baz-snow-ss/Voron-2.4-R2/Endstops/1eed2b93114540ddb6c84c9f8e0066f0.png

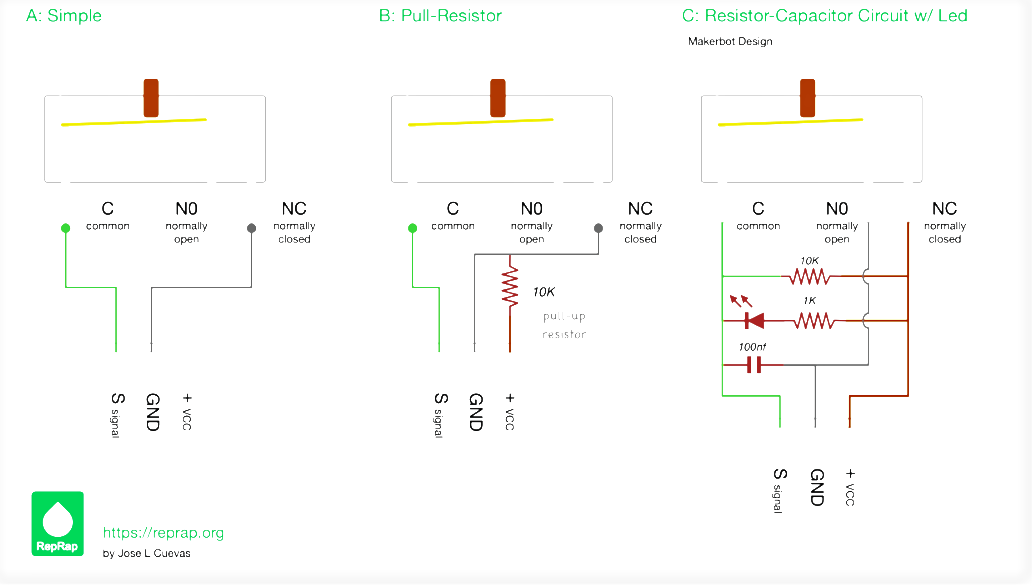
Endstops/1eed2b93114540ddb6c84c9f8e0066f0.png
