baz-snow-ss/Voron-2.4-R2/Endstops/c754031926eb4f4ea1a9c7ecbcfd5318.png

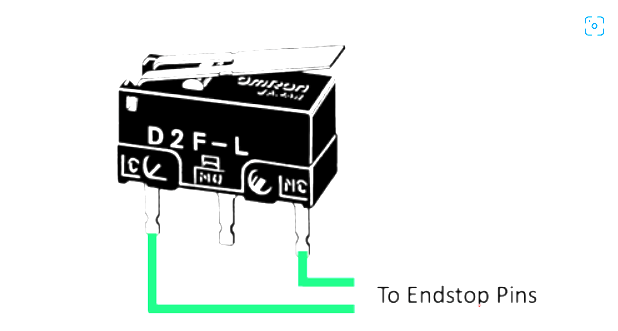
Endstops/c754031926eb4f4ea1a9c7ecbcfd5318.png
