baz-snow-ss/Voron-2.4-R2/Pictures/IMG20230324204420.jpg

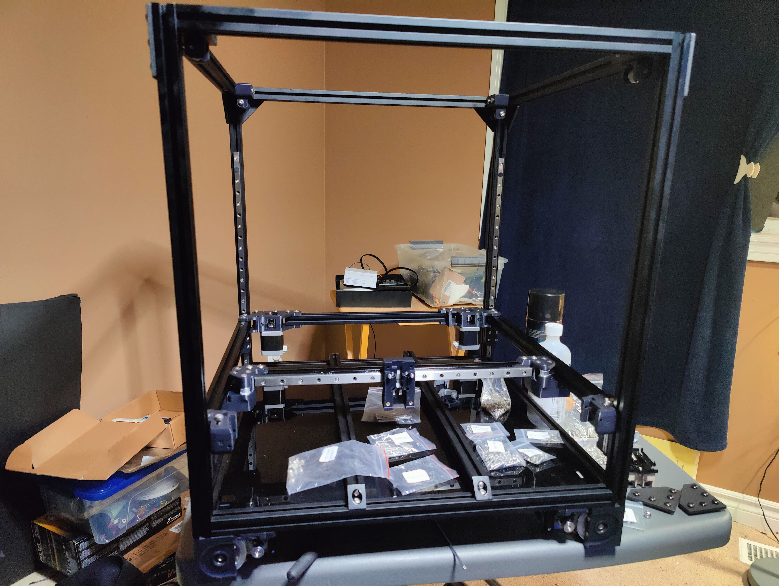
Pictures/IMG20230324204420.jpg
