baz-snow-ss/Voron-2.4-R2/Pictures/IMG20230408150425.jpg

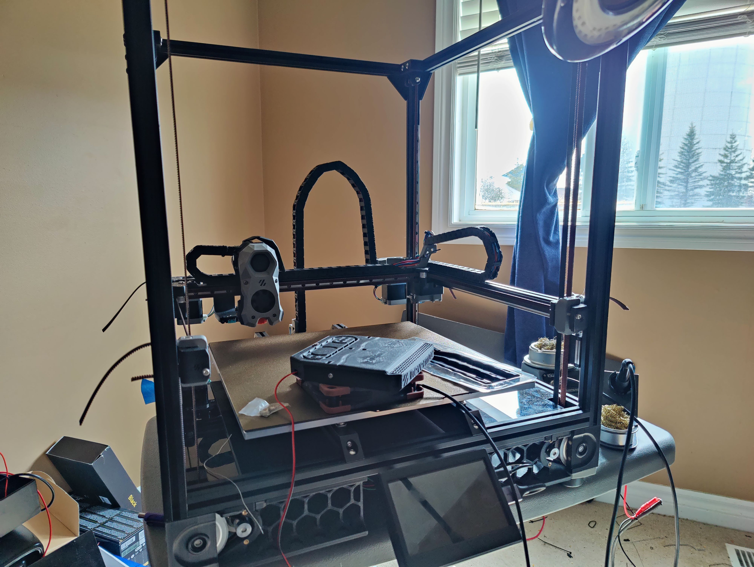
Pictures/IMG20230408150425.jpg
