baz-snow-ss/Voron-2.4-R2/Pictures/IMG20230410012818.jpg

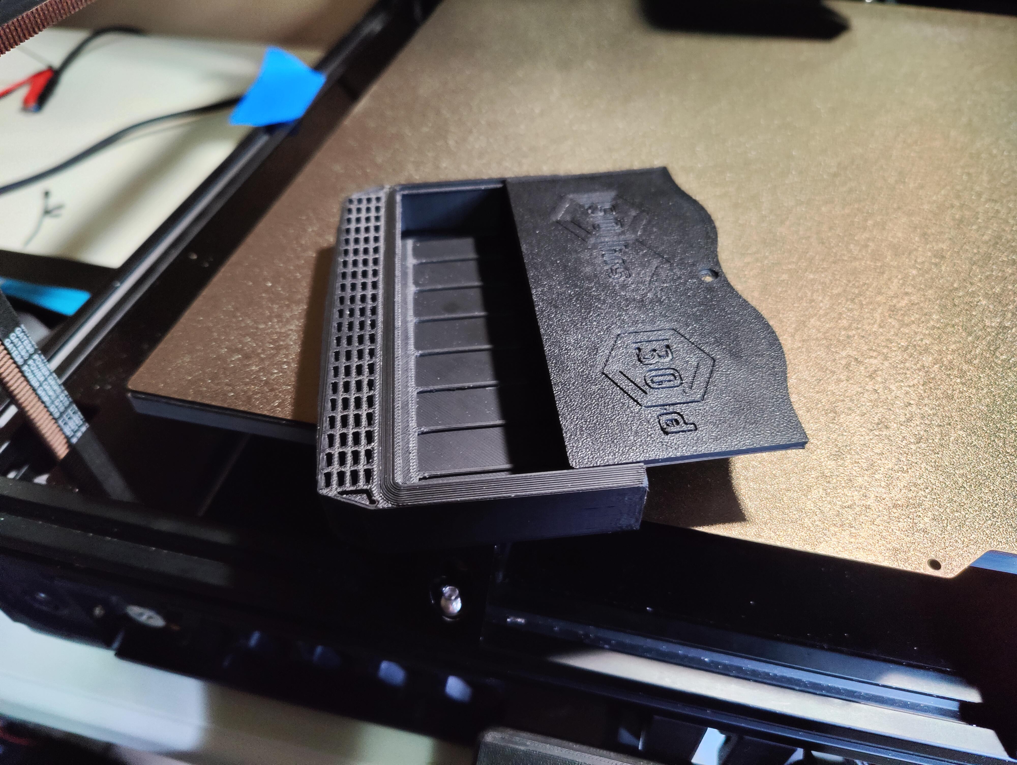
Pictures/IMG20230410012818.jpg
