baz-snow-ss/Voron-2.4-R2/Pictures/IMG20230410013023.jpg

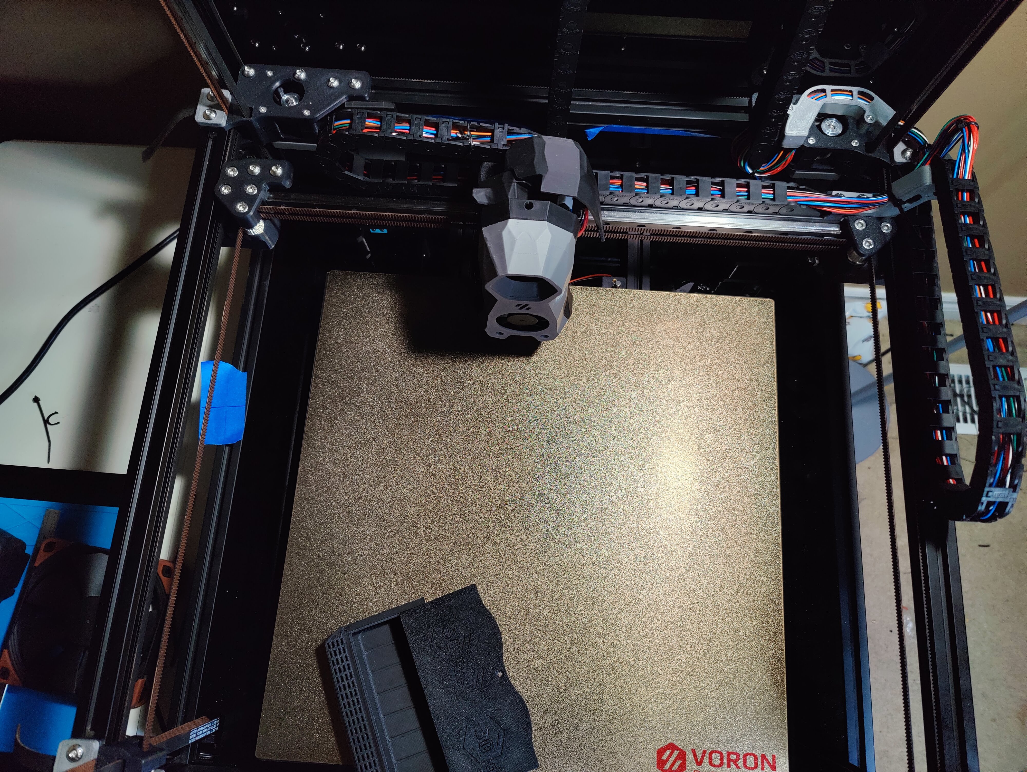
Pictures/IMG20230410013023.jpg
