baz-snow-ss/Voron-2.4-R2/Pictures/IMG20230415213202.jpg

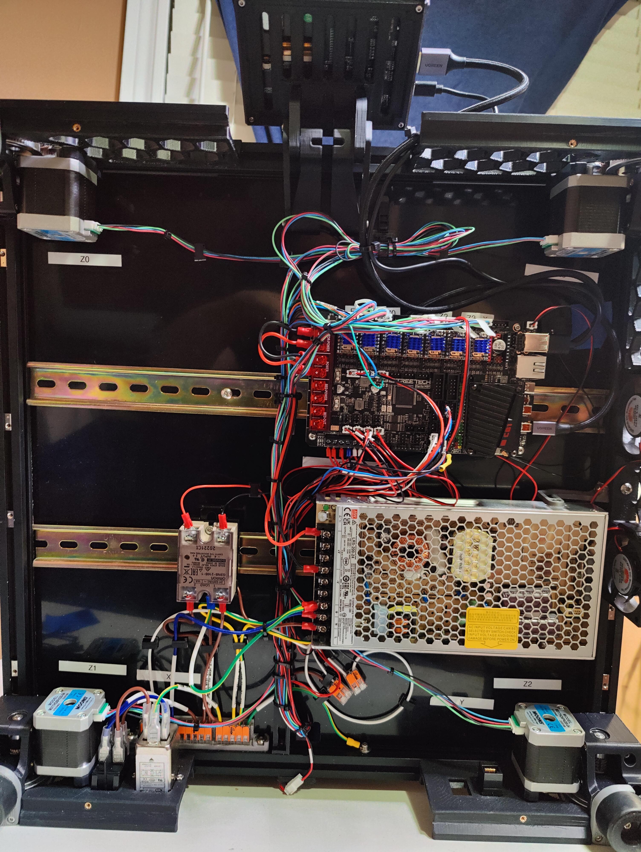
Pictures/IMG20230415213202.jpg
