baz-snow-ss/Voron-2.4-R2/Pictures/IMG20230418011041.jpg

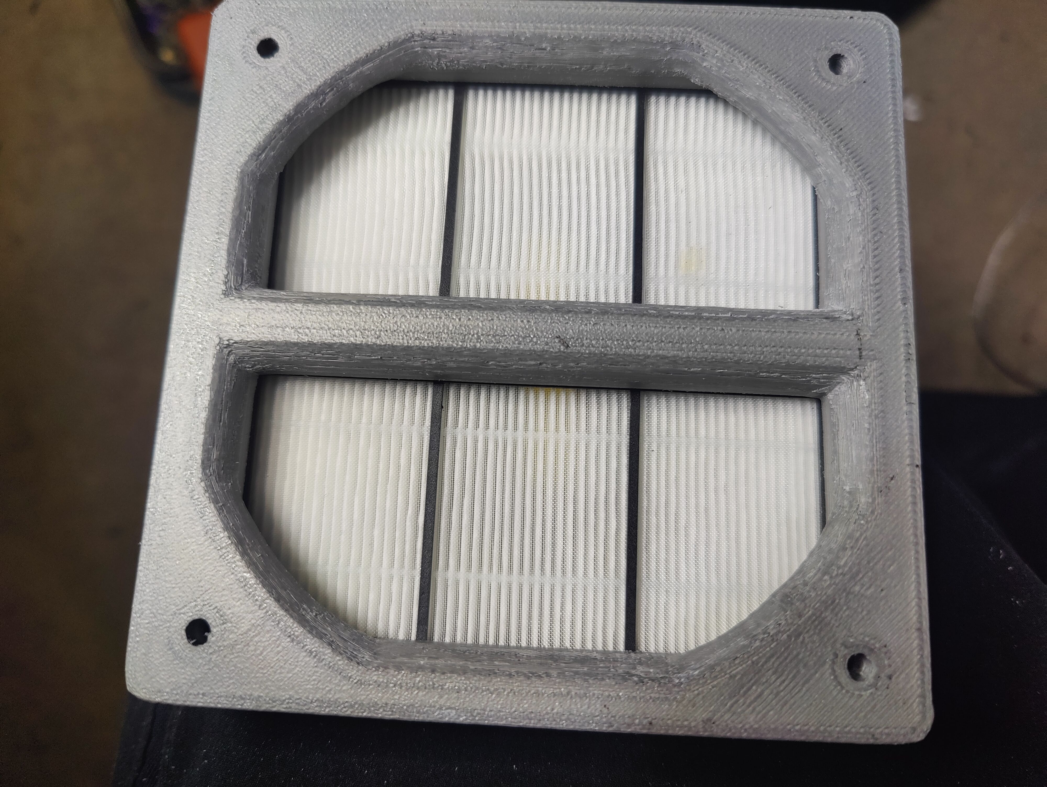
Pictures/IMG20230418011041.jpg
