baz-snow-ss/Voron-2.4-R2/Pictures/IMG20230419014356.jpg

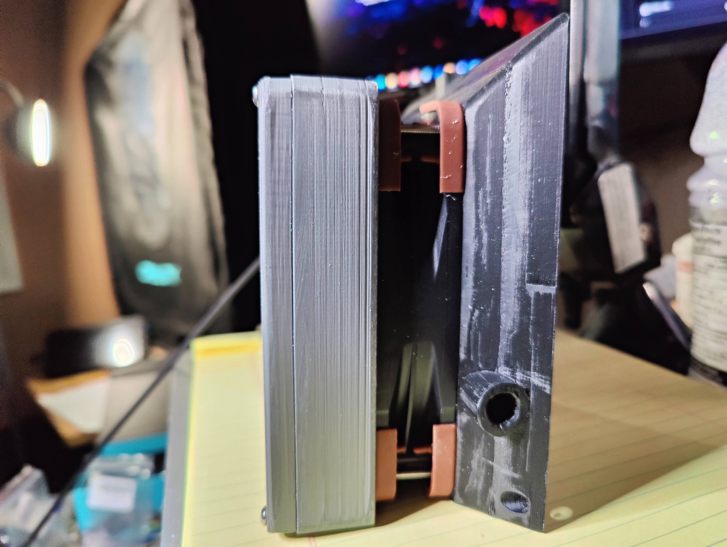
Pictures/IMG20230419014356.jpg
