baz-snow-ss/Voron-2.4-R2/Pictures/IMG20230423050257.jpg

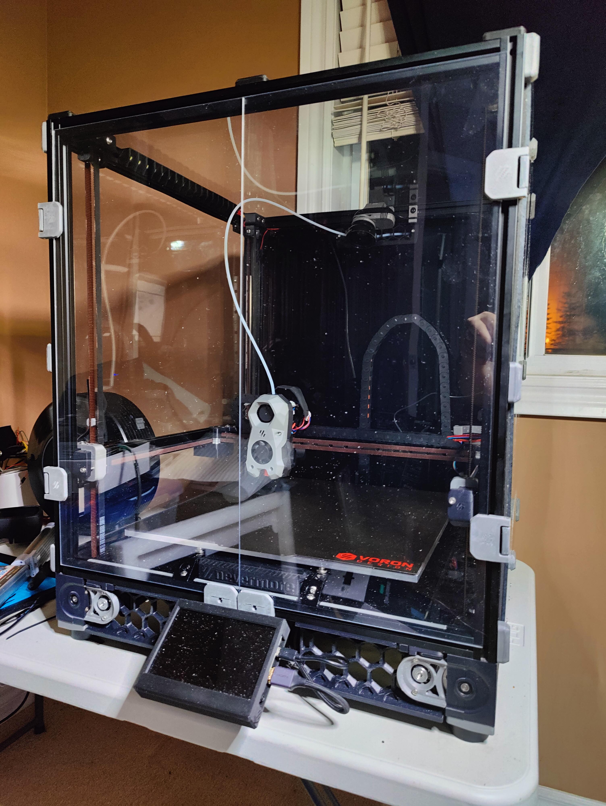
Pictures/IMG20230423050257.jpg
