baz-snow-ss/Voron-2.4-R2/Pictures/IMG20230423050415.jpg

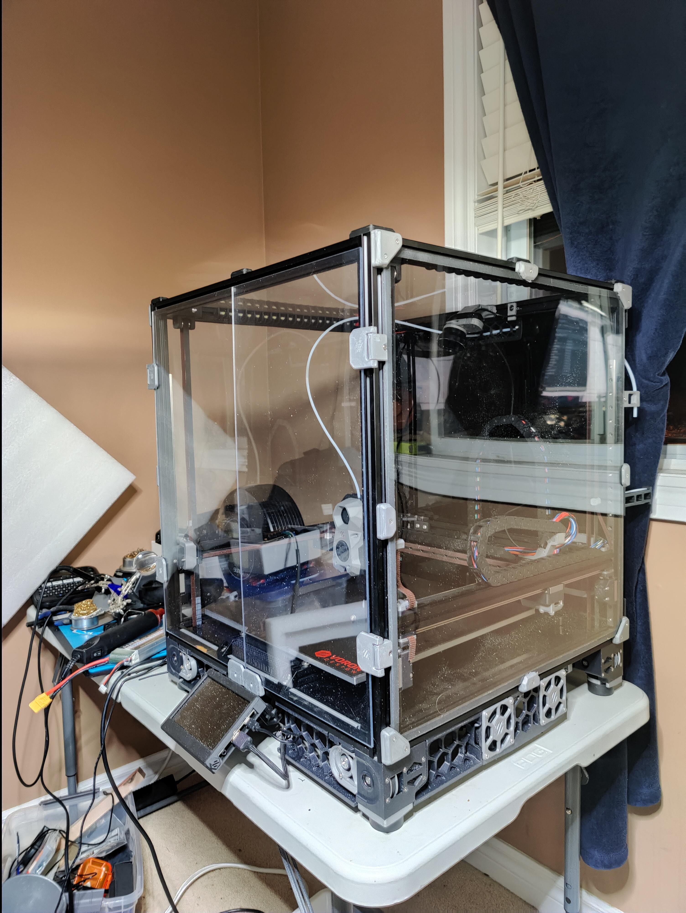
Pictures/IMG20230423050415.jpg
