baz-snow-ss/Voron-2.4-R2/Pictures/IMG20230425162826.jpg

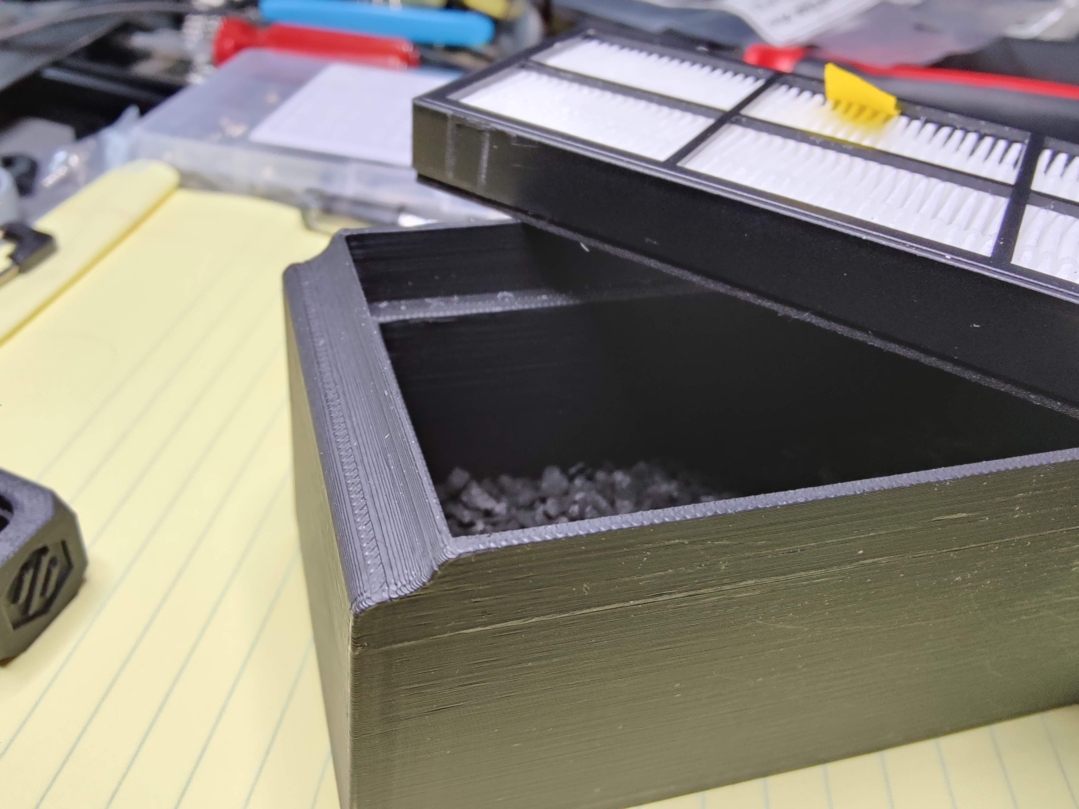
Pictures/IMG20230425162826.jpg
