baz-snow-ss/Voron-2.4-R2/Pictures/IMG20230511183152.jpg

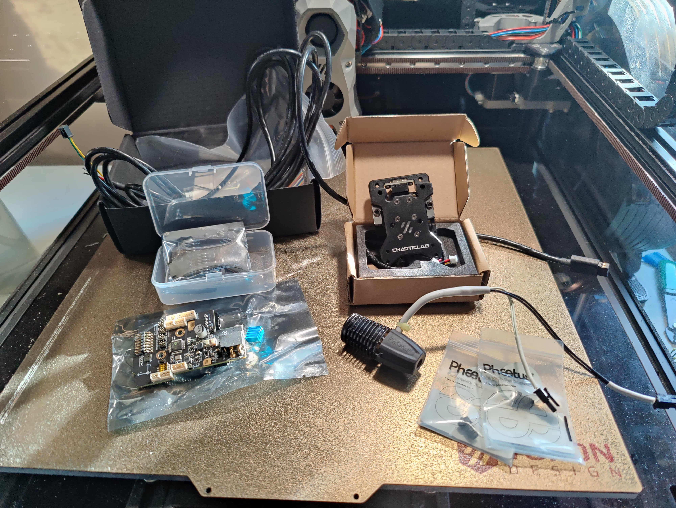
Pictures/IMG20230511183152.jpg
