baz-snow-ss/Voron-2.4-R2/STL/2020_Extrusion_profile_cover/images/395db7963a54a1277b0446aee03f2c51.jpg

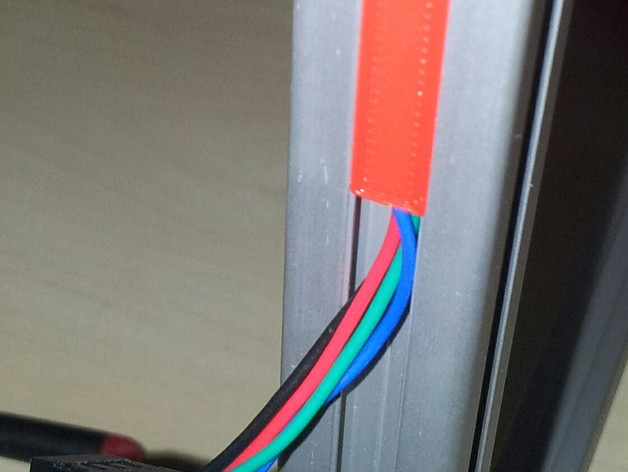
STL/2020_Extrusion_profile_cover/images/395db7963a54a1277b0446aee03f2c51.jpg
