baz-snow-ss/Voron-2.4-R2/STL/2020_Extrusion_profile_cover/images/Nut_6_Abdeckung_-_20.jpg

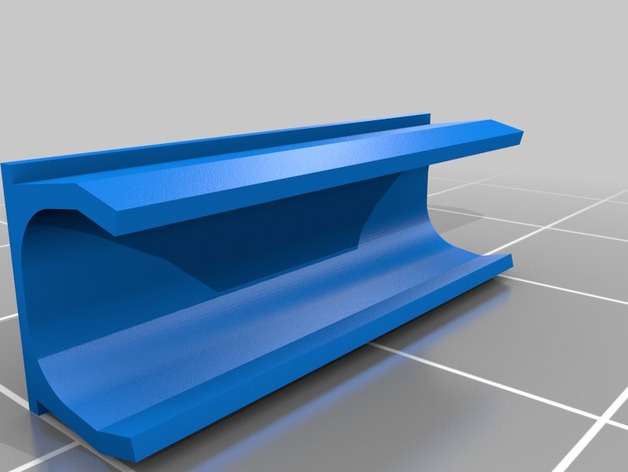
STL/2020_Extrusion_profile_cover/images/Nut_6_Abdeckung_-_20.jpg
