baz-snow-ss/Voron-2.4-R2/STL/Klicky-Probe-/Photos/klicky_base.jpg

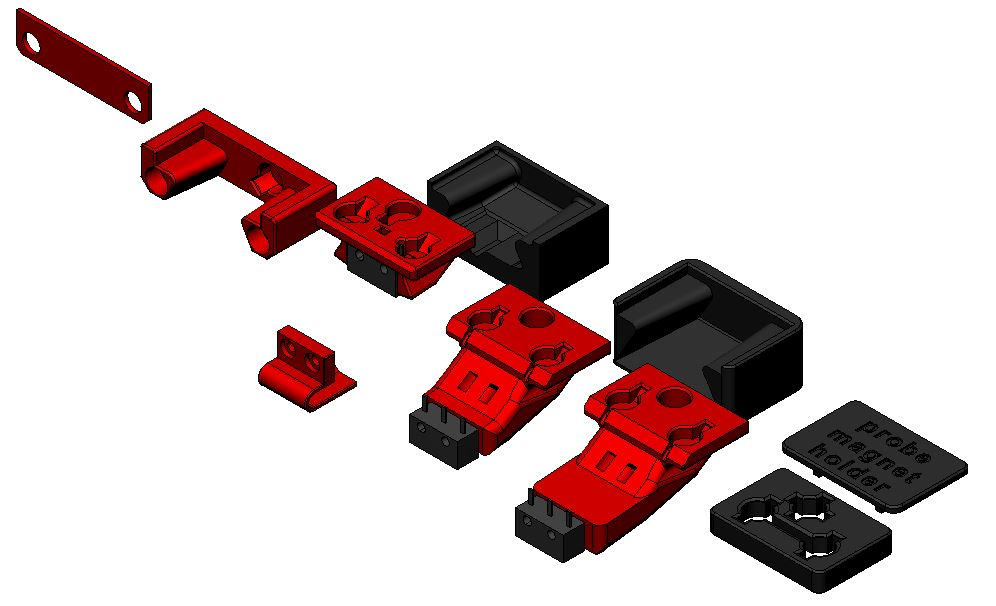
STL/Klicky-Probe-/Photos/klicky_base.jpg
