baz-snow-ss/Voron-2.4-R2/STL/LGX_Lite_Stealthburner_ERCF/IMAGES/IMG_02.png

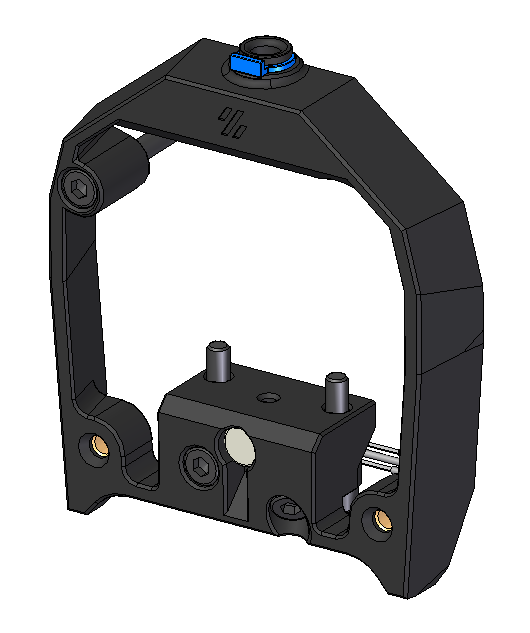
STL/LGX_Lite_Stealthburner_ERCF/IMAGES/IMG_02.png
