baz-snow-ss/Voron-2.4-R2/STL/Nevermore_Micro-master/images/DUO_COMBINED_render2.png

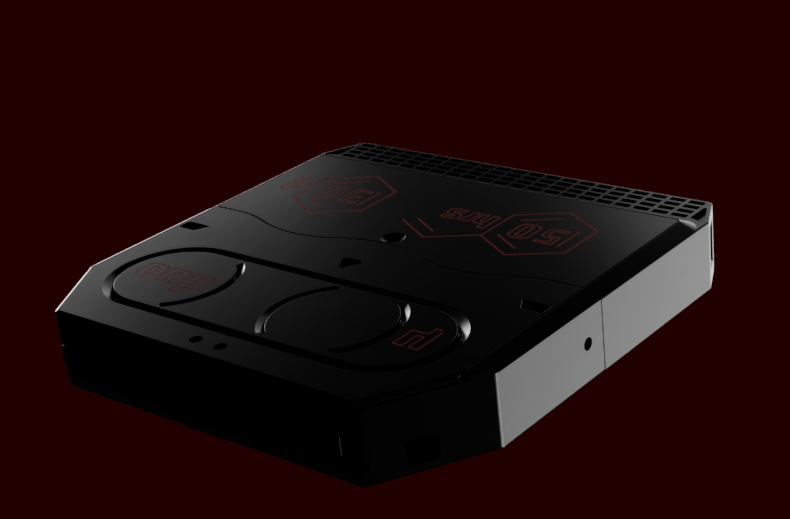
STL/Nevermore_Micro-master/images/DUO_COMBINED_render2.png
