baz-snow-ss/Voron-2.4-R2/STL/Nevermore_Micro-master/images/emitted-voc.jpg

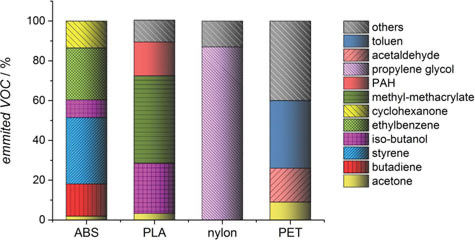
STL/Nevermore_Micro-master/images/emitted-voc.jpg
