baz-snow-ss/Voron-2.4-R2/STL/Nevermore_Micro-master/images/Nevermore_Micro3.png

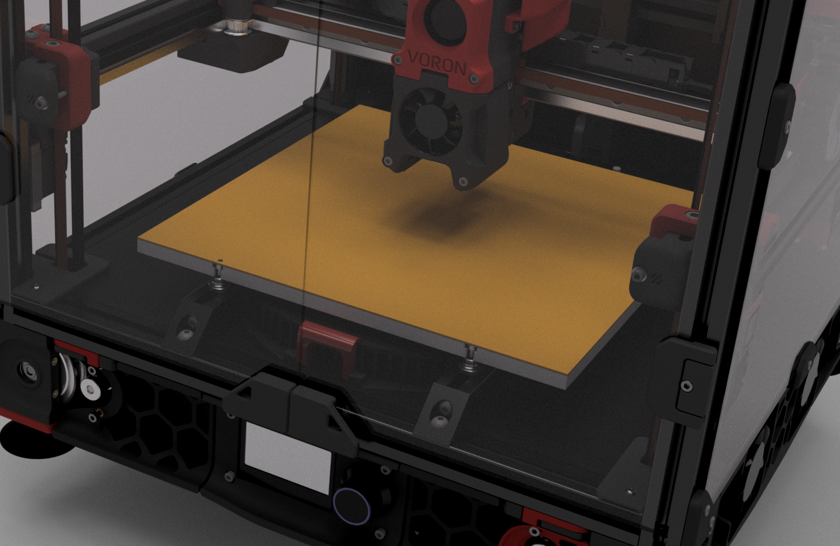
STL/Nevermore_Micro-master/images/Nevermore_Micro3.png
