baz-snow-ss/Voron-2.4-R2/STL/Nevermore_Micro-master/images/voron2-oxidation1.png

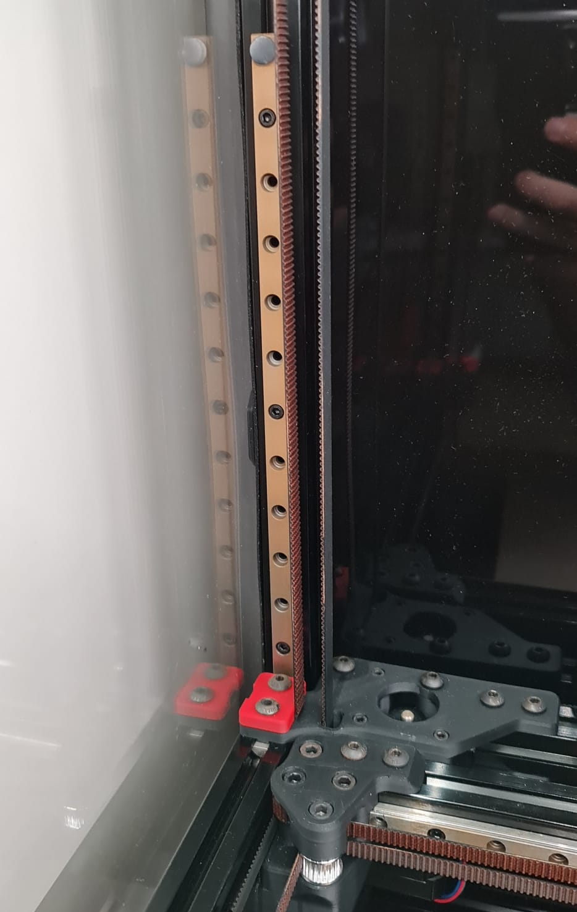
STL/Nevermore_Micro-master/images/voron2-oxidation1.png
