baz-snow-ss/Voron-2.4-R2/STL/Nevermore_Micro-master/images/voron-v0.jpg

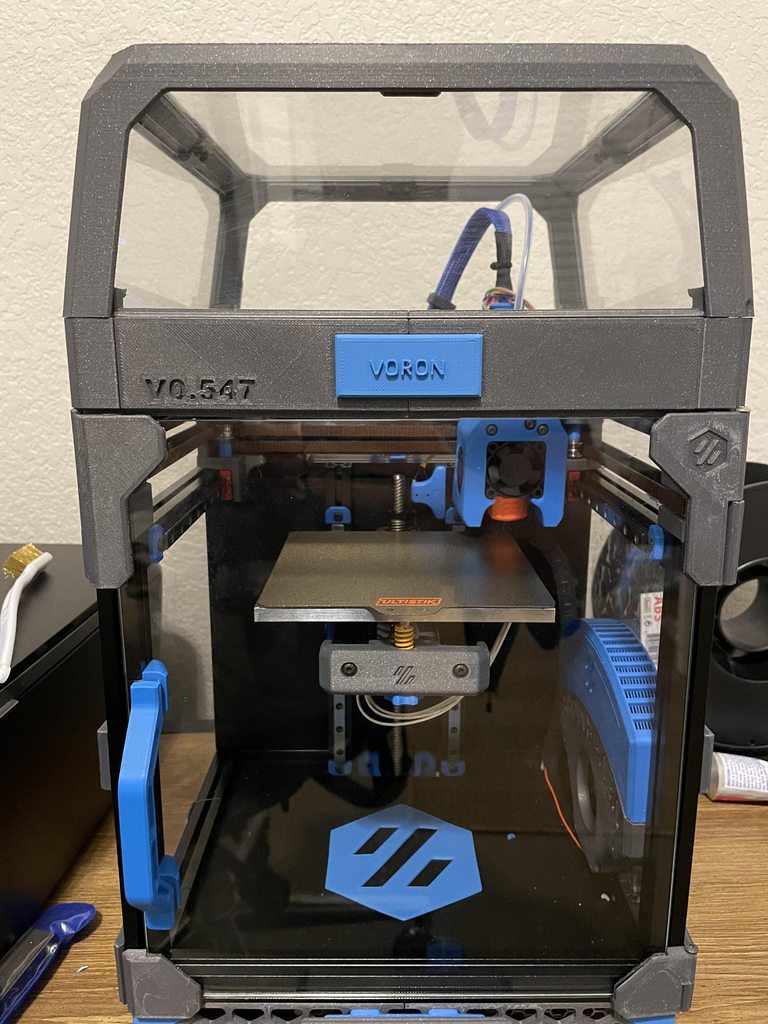
STL/Nevermore_Micro-master/images/voron-v0.jpg
