baz-snow-ss/Voron-2.4-R2/STL/Nevermore_Micro-master/V5_Duo/Mods/RLF-35_by_Rama/12.jpg

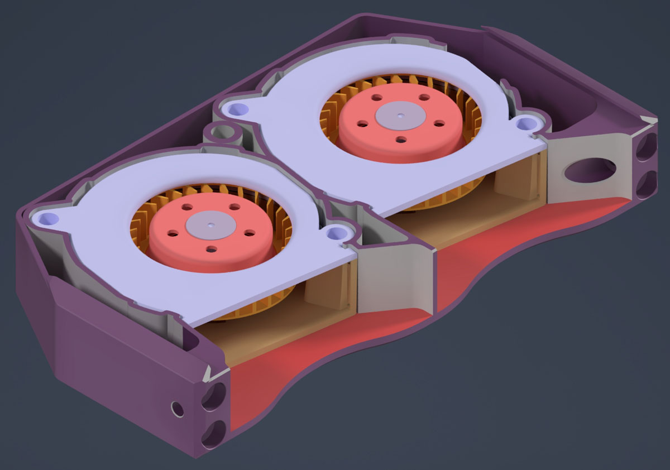
STL/Nevermore_Micro-master/V5_Duo/Mods/RLF-35_by_Rama/12.jpg
