baz-snow-ss/Voron-2.4-R2/STL/Nevermore_Micro-master/V5_Duo/Mods/RLF-35_Wago_&_Less-Plastic_by-Rick/wago_rlf.jpg

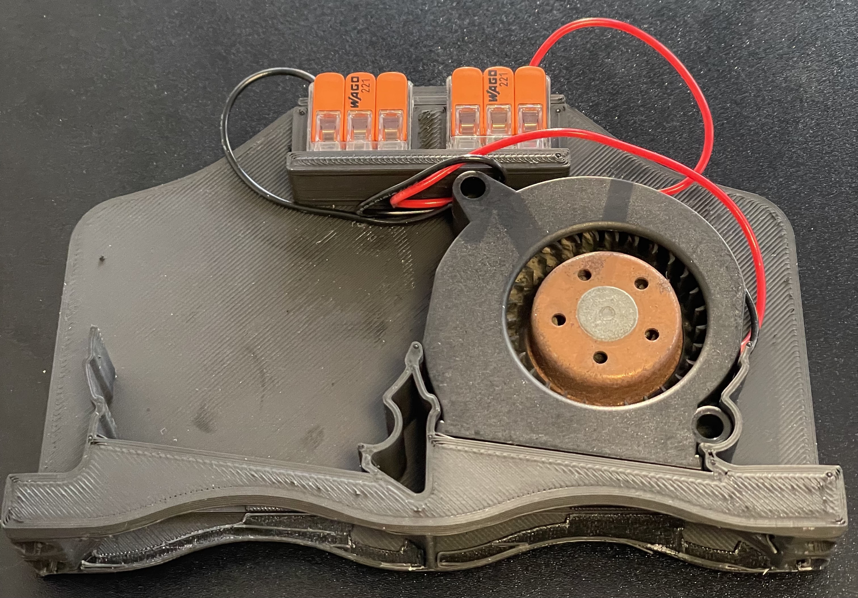
STL/Nevermore_Micro-master/V5_Duo/Mods/RLF-35_Wago_&_Less-Plastic_by-Rick/wago_rlf.jpg
