baz-snow-ss/Voron-2.4-R2/STL/Nevermore_Micro-master/V5_Duo/Mods/Slide-in-Magnets_by-ChainsDD/nevermore_3.jpg

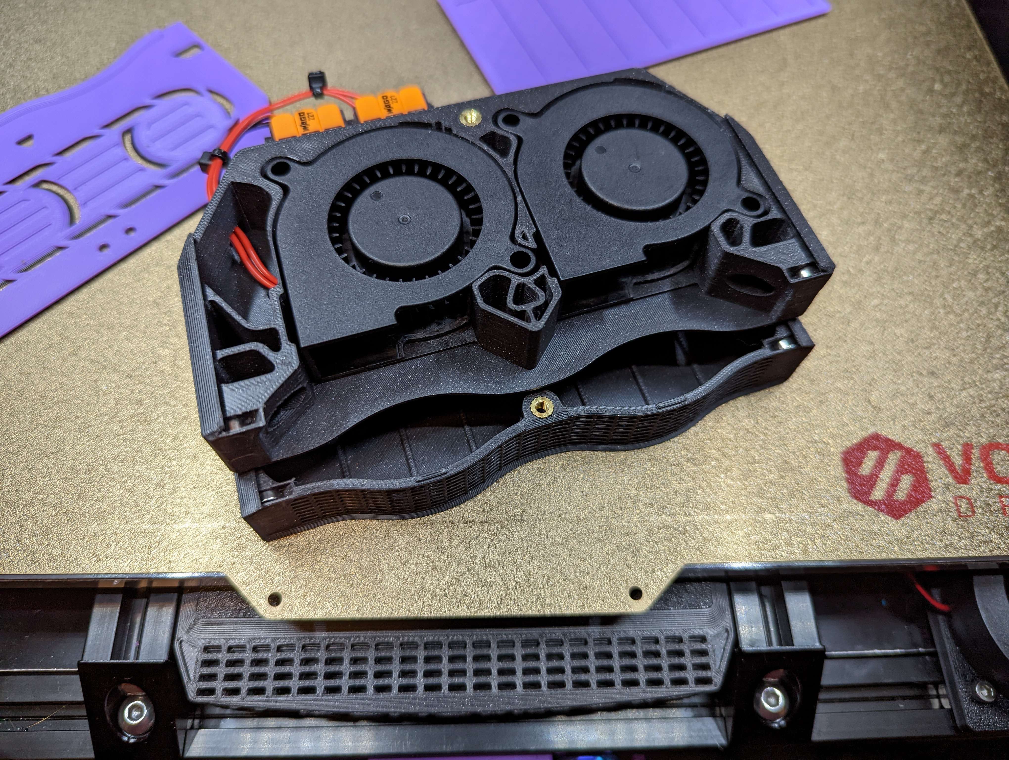
STL/Nevermore_Micro-master/V5_Duo/Mods/Slide-in-Magnets_by-ChainsDD/nevermore_3.jpg
