baz-snow-ss/Voron-2.4-R2/STL/Voron 2.4 r2 GE5C Bearing/Images/3.png

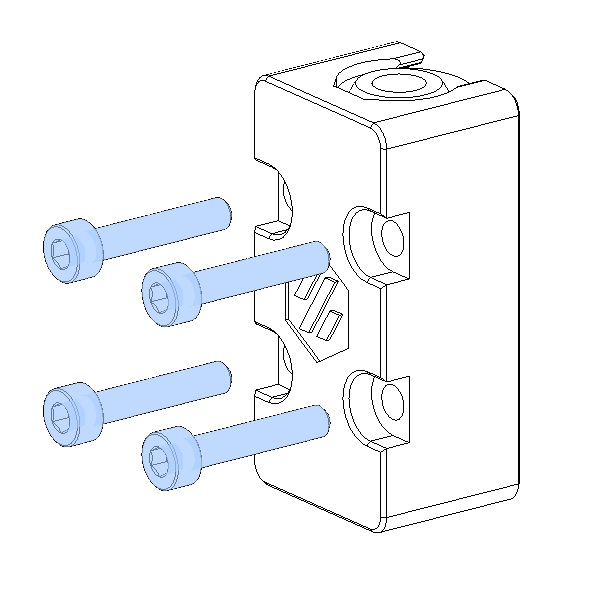
STL/Voron 2.4 r2 GE5C Bearing/Images/3.png
