baz-snow-ss/Voron-2.4-R2/STL/Nevermore_Micro-master/V5_Duo/Mods/Slide-in-Magnets_by-ChainsDD/Duo_Plenum.step

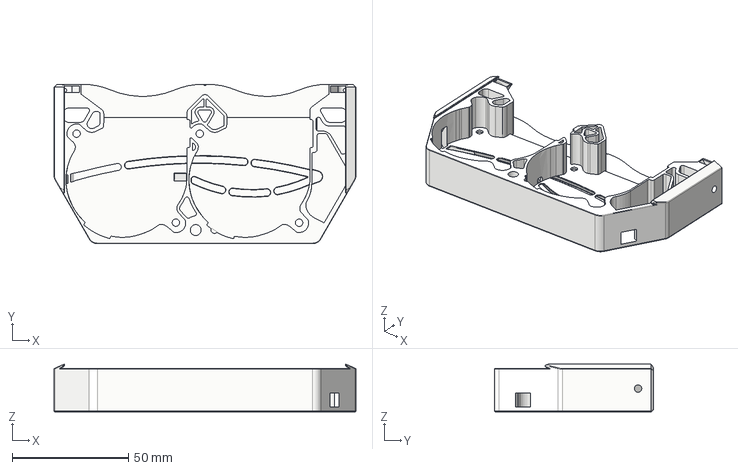
[picture p90: CAD file, 2023-06-08]
STL/Nevermore_Micro-master/V5_Duo/Mods/Slide-in-Magnets_by-ChainsDD/Duo_Plenum.step
130.0 x 68.6 x 20.5 mm
