baz-snow-ss/Voron-2.4-R2/STL/Nevermore_Micro-master/V5_Duo/V2/V2_Duo_Plenum.stl

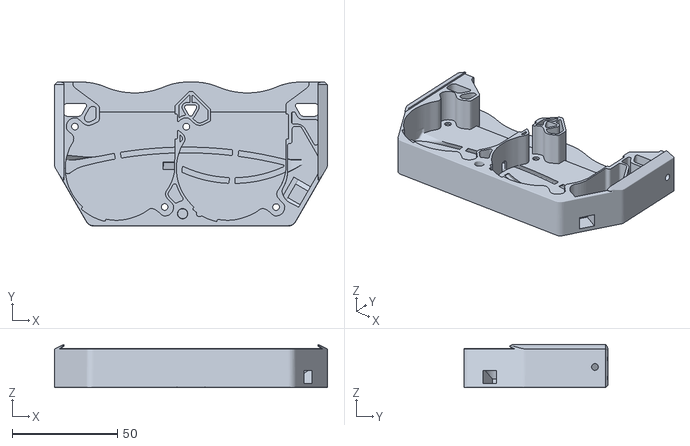
[picture p91: CAD file, 2023-06-08]
STL/Nevermore_Micro-master/V5_Duo/V2/V2_Duo_Plenum.stl
130.0 x 68.6 x 20.6
