baz-snow-ss/Voron-2.4-R2/STL/stealthburner-lgx-lite-ebb-2209-2240-remix-model_files/LGX_LITE_EBB_22xx_mod.3mf

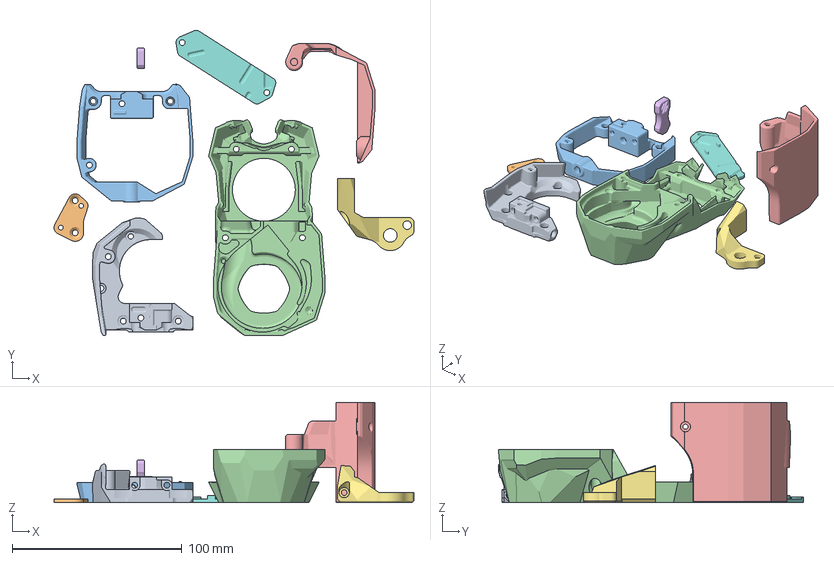
[picture p92: CAD file, 2023-06-07]
STL/stealthburner-lgx-lite-ebb-2209-2240-remix-model_files/LGX_LITE_EBB_22xx_mod.3mf
212.1 x 179.9 x 59.0 mm
Rear_body_LGX_Lite_Stealthburner_ERCF_Released_rev01
EBB 22xx to LGX Lite Adapter
Frontbody_LGX_lite_EBB_SB22xx
Print Orientation Assembly_1
LGX_lite_fan_cable_cover_EBB_22xx
[a]_Tension_rocker_LGX_Lite_Stealthburner_ERCF_rev01
LGX_lite_umbilical_anchor v1
EBB 0000 Mounting Plate
