baz-snow-ss/Voron-2.4-R2/STL/Voron 2.4 r2 GE5C Bearing/STLs/[a]_z_belt_clamp_lower_x4.stl

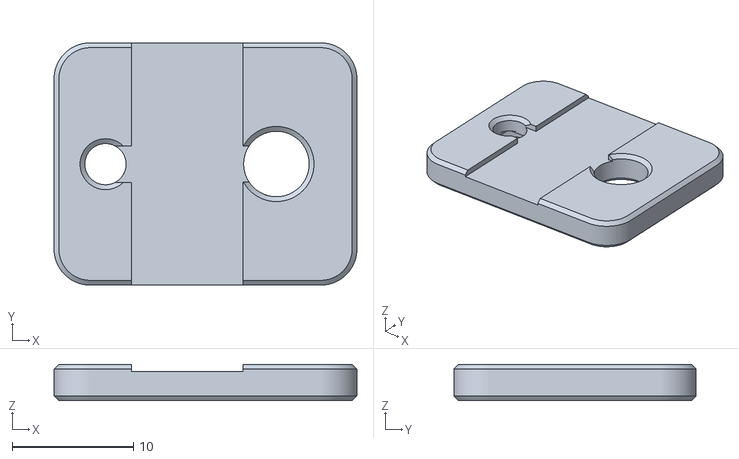
[picture p93: CAD file, 2023-06-08]
STL/Voron 2.4 r2 GE5C Bearing/STLs/[a]_z_belt_clamp_lower_x4.stl
25.0 x 20.0 x 3.00
