baz-snow-ss/Voron-2.4-R2/STL/Voron 2.4 r2 GE5C Bearing/STLs/Z_Joints/z_joint_ge5c_igus_eglm-05_x4.stl

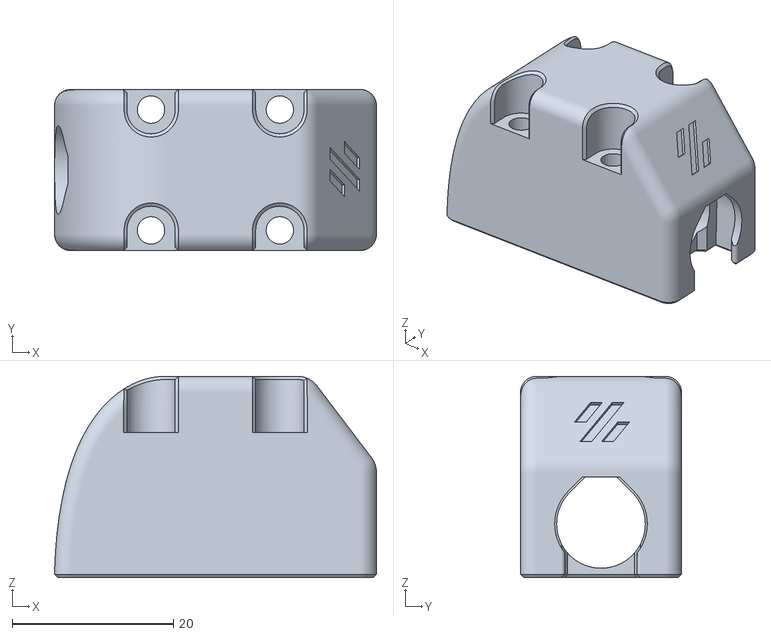
[picture p94: CAD file, 2023-06-08]
STL/Voron 2.4 r2 GE5C Bearing/STLs/Z_Joints/z_joint_ge5c_igus_eglm-05_x4.stl
40.0 x 20.0 x 25.0
