baz-snow-ss/Voron-2.4-R2/STL/Klicky-Probe-/Base_STL/Base_STL/Probe_magnet_holder.stl

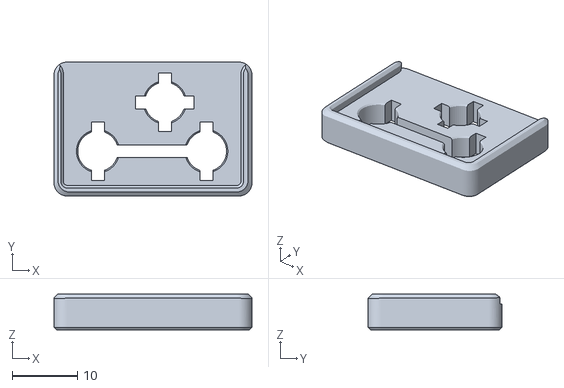
[picture p95: CAD file, 2023-06-08]
STL/Klicky-Probe-/Base_STL/Base_STL/Probe_magnet_holder.stl
30.4 x 20.6 x 5.50
