baz-snow-ss/Voron-2.4-R2/STL/LGX Stealthburner/sb2040_fan_cover (1).stl

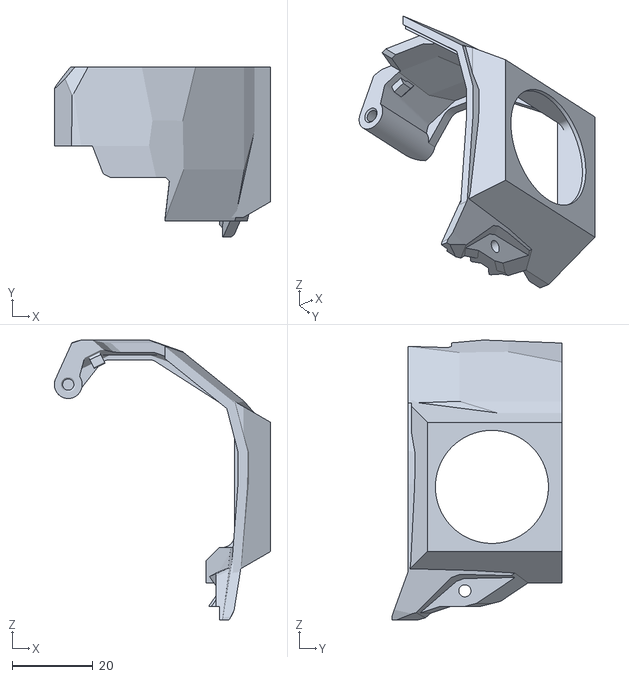
[picture p96: CAD file, 2023-06-07]
STL/LGX Stealthburner/sb2040_fan_cover (1).stl
53.6 x 42.2 x 69.4
