baz-snow-ss/Voron-2.4-R2/STL/LGX_Lite_Stealthburner_ERCF/STL/Rear_body_LGX_Lite_Stealthburner_ERCF_Released_rev01.stl

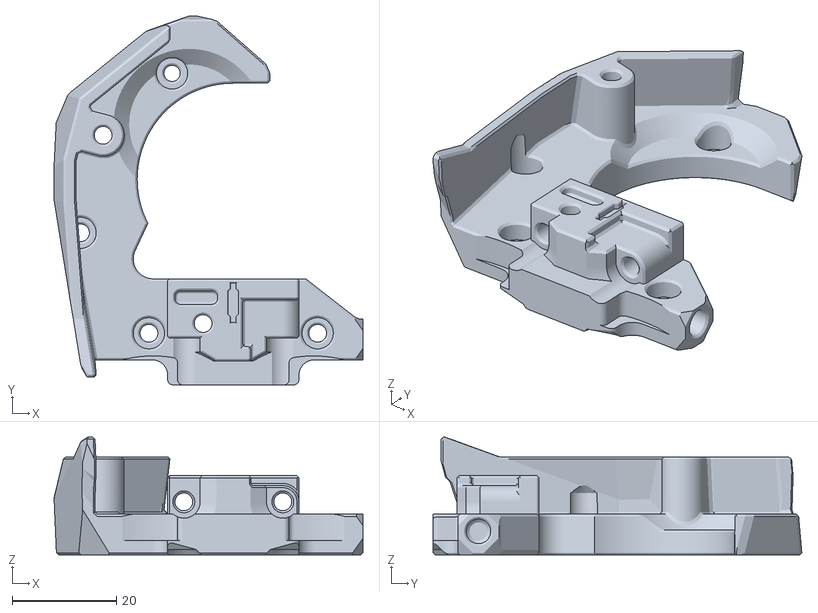
[picture p97: CAD file, 2023-06-07]
STL/LGX_Lite_Stealthburner_ERCF/STL/Rear_body_LGX_Lite_Stealthburner_ERCF_Released_rev01.stl
59.3 x 70.8 x 22.6
