baz-snow-ss/Voron-2.4-R2/STL/logitech-c270/focus_ring.step

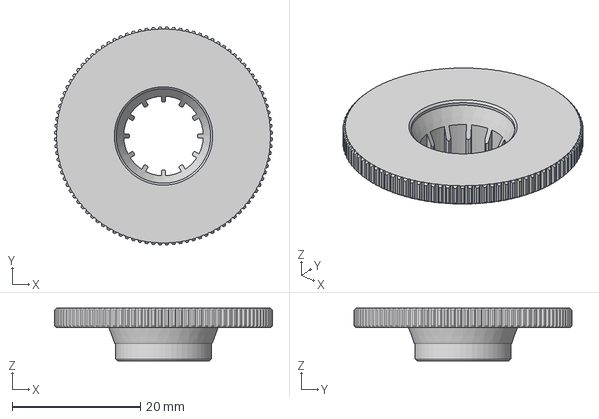
[picture p98: CAD file, 2023-06-07]
STL/logitech-c270/focus_ring.step
34.0 x 34.0 x 8.20 mm
