baz-snow-ss/Voron-2.4-R2/STL/Nevermore_Micro-master/V4/BASE_V0_1515.stl

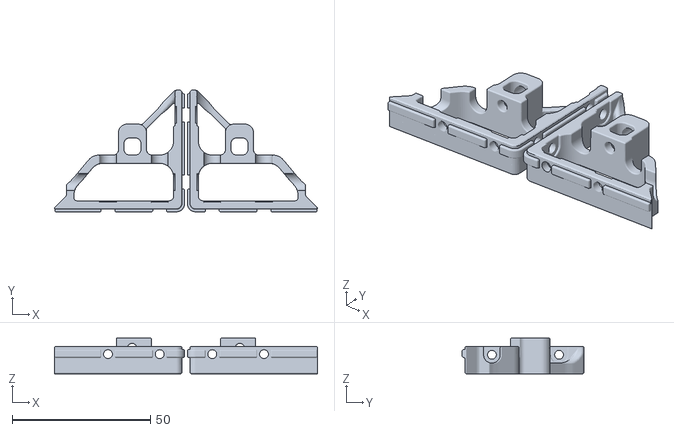
[picture p99: CAD file, 2023-06-08]
STL/Nevermore_Micro-master/V4/BASE_V0_1515.stl
95.0 x 44.0 x 13.0
