baz-snow-ss/Voron-2.4-R2/STL/Nevermore_Micro-master/V4/V4_4x6_magnets/base_fix.stl

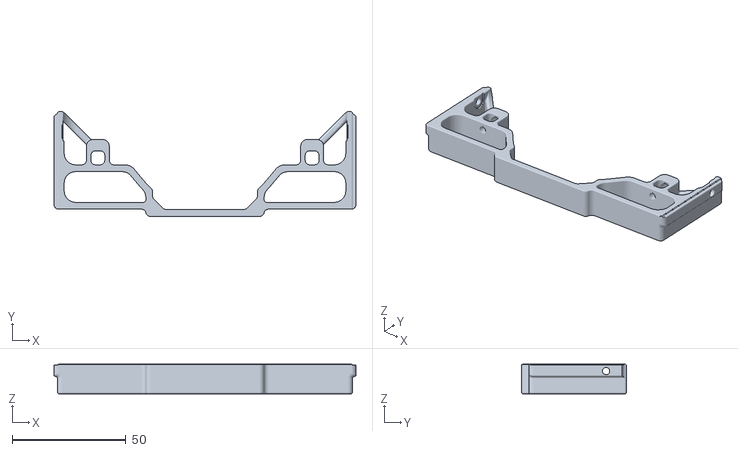
[picture p100: CAD file, 2023-06-08]
STL/Nevermore_Micro-master/V4/V4_4x6_magnets/base_fix.stl
133.0 x 46.2 x 13.0
