baz-snow-ss/Voron-2.4-R2/STL/Nevermore_Micro-master/V4/V4_6x3_magnets/FILTER_CARTRIDGE_LID_6_3.stl

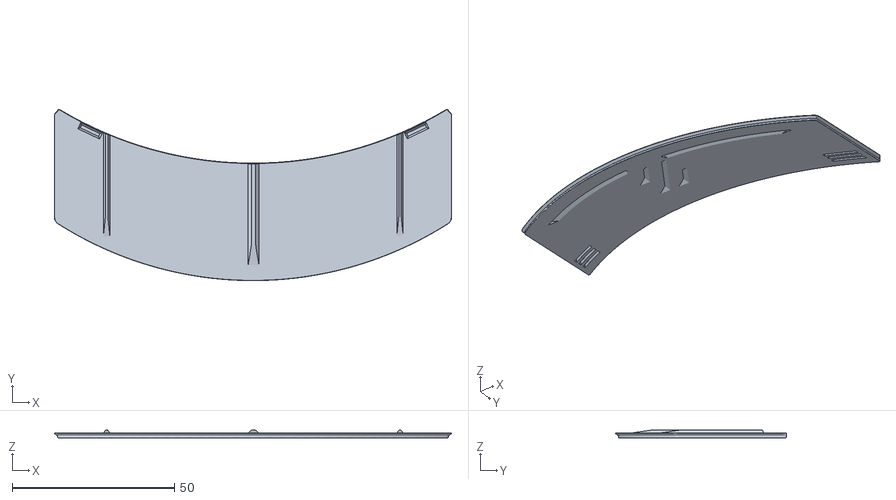
[picture p101: CAD file, 2023-06-08]
STL/Nevermore_Micro-master/V4/V4_6x3_magnets/FILTER_CARTRIDGE_LID_6_3.stl
122.5 x 52.8 x 2.34
