baz-snow-ss/Voron-2.4-R2/STL/Nevermore_Micro-master/V5_Duo/Duo_Plenum_RC7_DELTA.stl

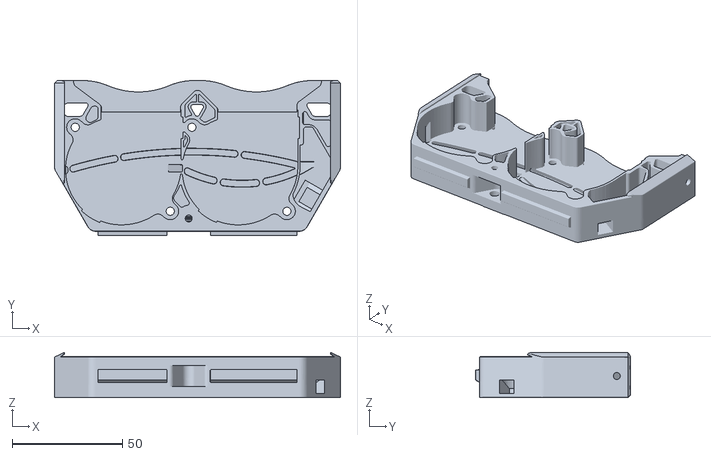
[picture p102: CAD file, 2023-06-08]
STL/Nevermore_Micro-master/V5_Duo/Duo_Plenum_RC7_DELTA.stl
130.0 x 70.5 x 20.6
