baz-snow-ss/Voron-2.4-R2/STL/Voron 2.4 r2 GE5C Bearing/STLs/Z_Joints/z_joint_igus_kglm-05_x4.stl

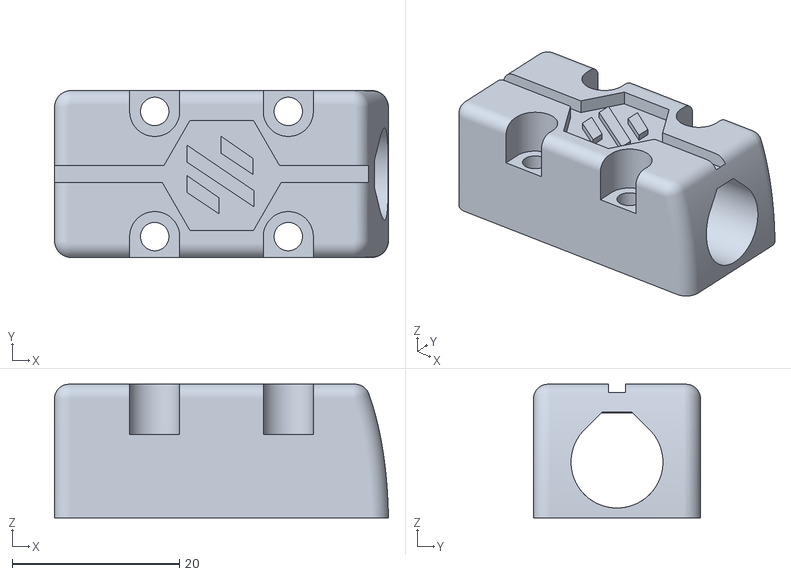
[picture p103: CAD file, 2023-06-08]
STL/Voron 2.4 r2 GE5C Bearing/STLs/Z_Joints/z_joint_igus_kglm-05_x4.stl
40.0 x 20.0 x 16.0
