baz-snow-ss/Voron-2.4-R2/STL/Klicky-Probe-/Base_STL/Base_STL/KlickyProbe_Long_v2.stl

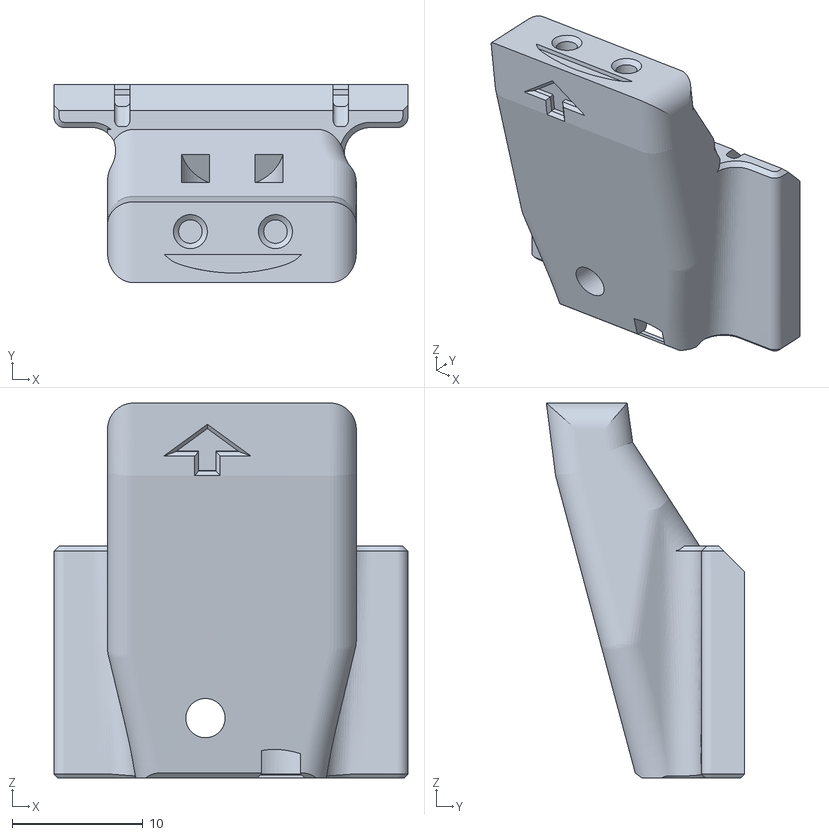
[picture p104: CAD file, 2023-06-08]
STL/Klicky-Probe-/Base_STL/Base_STL/KlickyProbe_Long_v2.stl
27.0 x 15.1 x 28.6
