baz-snow-ss/Voron-2.4-R2/STL/Klicky-Probe-/Base_STL/KlickyProbe_Longer_v2.stl

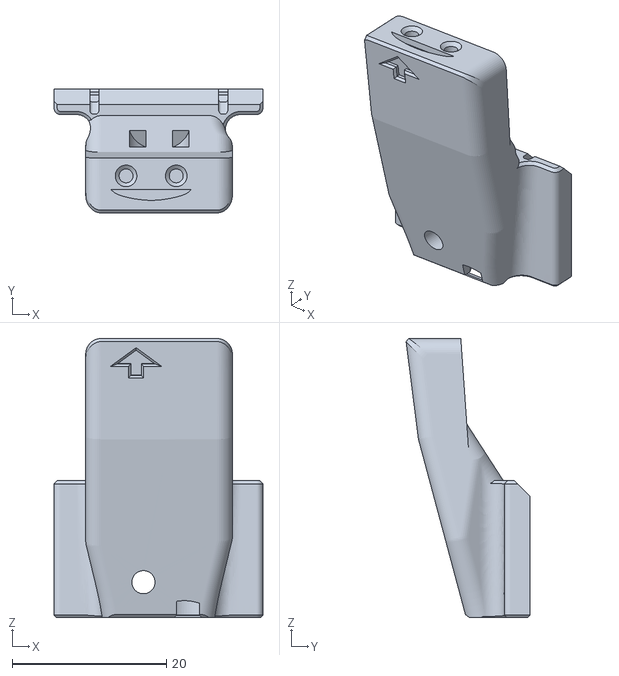
[picture p105: CAD file, 2023-06-08]
STL/Klicky-Probe-/Base_STL/KlickyProbe_Longer_v2.stl
27.0 x 16.0 x 36.1
