baz-snow-ss/Voron-2.4-R2/STL/LGX Stealthburner/Mountable_Filament_Sensor.stl

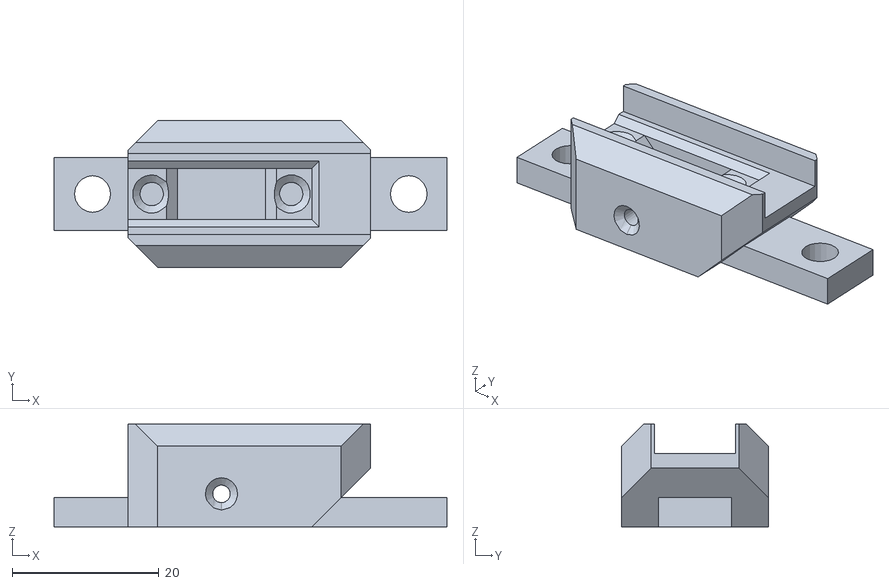
[picture p106: CAD file, 2023-06-07]
STL/LGX Stealthburner/Mountable_Filament_Sensor.stl
53.5 x 20.0 x 14.0
