baz-snow-ss/Voron-2.4-R2/STL/LGX_Lite_Stealthburner_ERCF/STL/Front_body_LGX_Lite_Stealthburner_ERCF_Released_rev01.stl

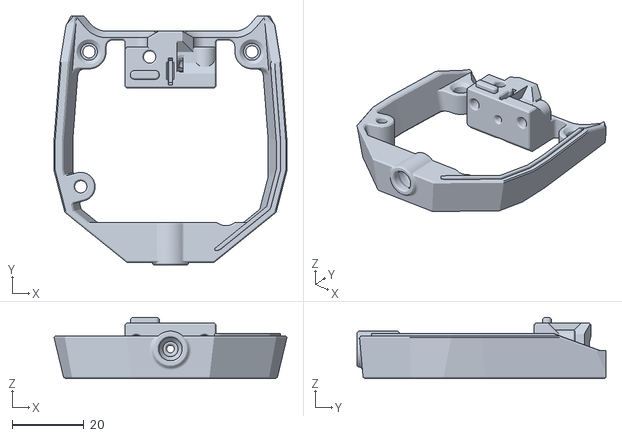
[picture p107: CAD file, 2023-06-07]
STL/LGX_Lite_Stealthburner_ERCF/STL/Front_body_LGX_Lite_Stealthburner_ERCF_Released_rev01.stl
64.9 x 69.4 x 17.0
