baz-snow-ss/Voron-2.4-R2/STL/logitech-c270/case_back_with_vents.stl

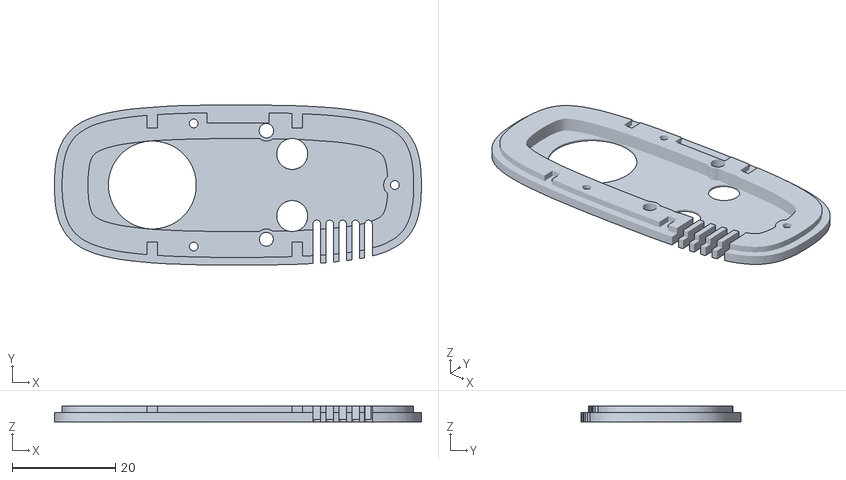
[picture p108: CAD file, 2023-06-07]
STL/logitech-c270/case_back_with_vents.stl
71.0 x 31.0 x 3.00
