baz-snow-ss/Voron-2.4-R2/STL/Nevermore_Micro-master/V4/BASES_V1.stl

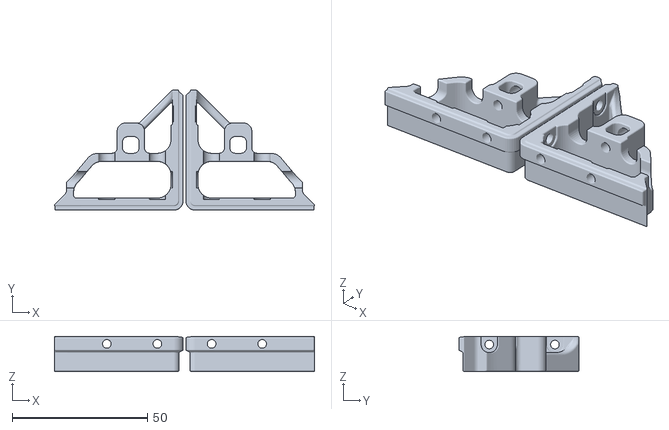
[picture p109: CAD file, 2023-06-08]
STL/Nevermore_Micro-master/V4/BASES_V1.stl
96.0 x 44.5 x 13.0
