baz-snow-ss/Voron-2.4-R2/STL/Nevermore_Micro-master/V4/V4_4x6_magnets/FAN_PLENUM_LID_4_6_by_Dom186.stl

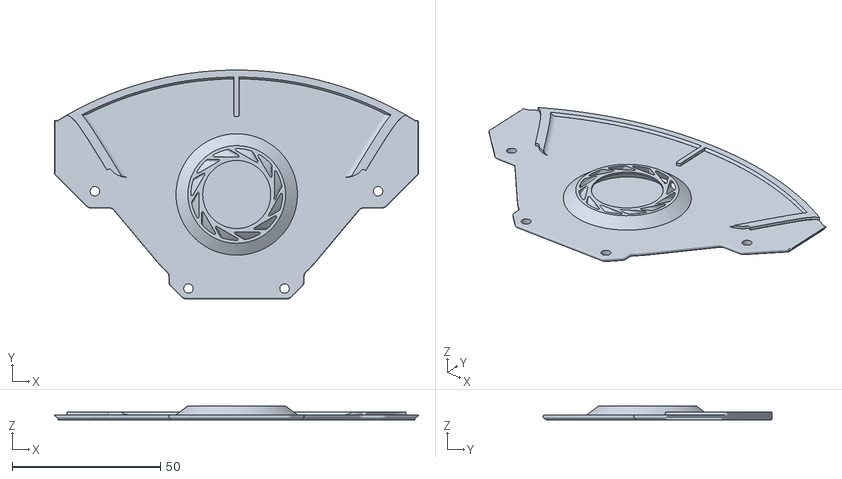
[picture p110: CAD file, 2023-06-08]
STL/Nevermore_Micro-master/V4/V4_4x6_magnets/FAN_PLENUM_LID_4_6_by_Dom186.stl
123.0 x 77.3 x 4.80
