baz-snow-ss/Voron-2.4-R2/STL/Nevermore_Micro-master/V5_Duo/1.8/1,8_Frame_Connector.stl

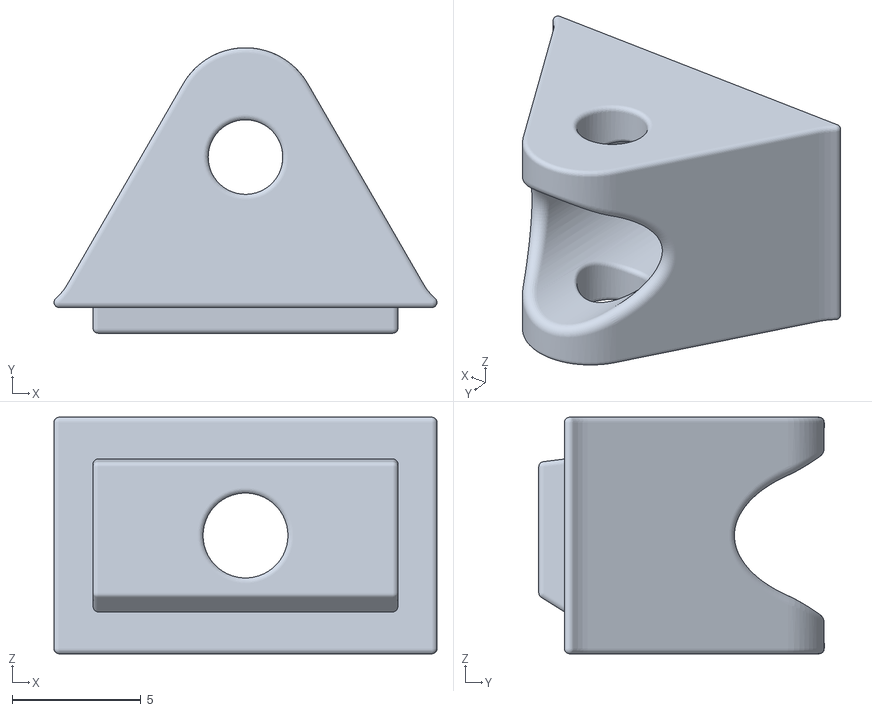
[picture p111: CAD file, 2023-06-08]
STL/Nevermore_Micro-master/V5_Duo/1.8/1,8_Frame_Connector.stl
14.9 x 11.1 x 9.20
