baz-snow-ss/Voron-2.4-R2/STL/Nevermore_Micro-master/V5_Duo/Mods/Slide-in-Magnets_by-ChainsDD/Duo_Plenum_Wago.step

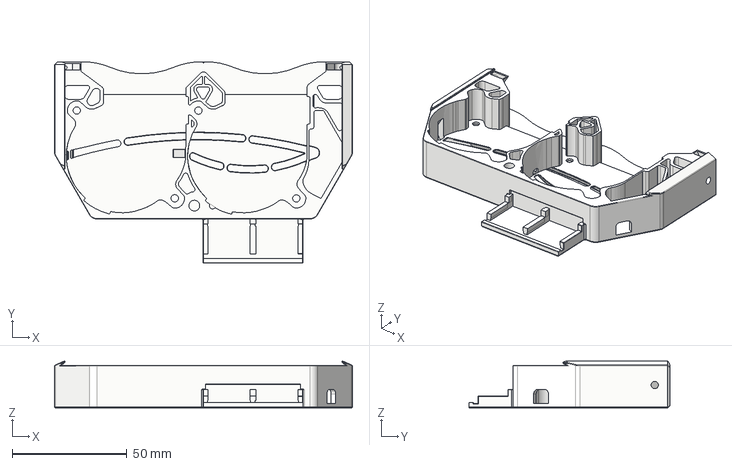
[picture p112: CAD file, 2023-06-08]
STL/Nevermore_Micro-master/V5_Duo/Mods/Slide-in-Magnets_by-ChainsDD/Duo_Plenum_Wago.step
130.0 x 87.8 x 20.5 mm
