baz-snow-ss/Voron-2.4-R2/STL/Nevermore_Micro-master/V5_Duo/V2/Duo_XL_Cartridge_LID.stl

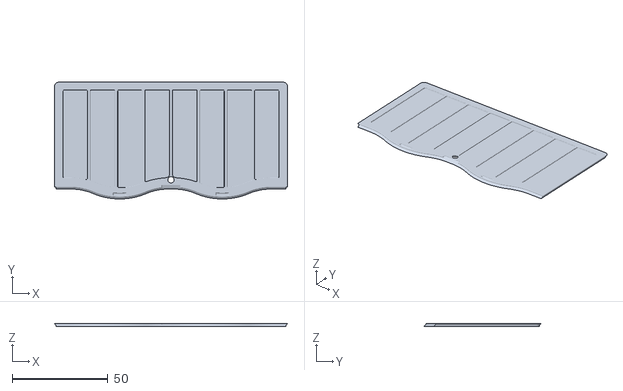
[picture p113: CAD file, 2023-06-08]
STL/Nevermore_Micro-master/V5_Duo/V2/Duo_XL_Cartridge_LID.stl
122.0 x 61.2 x 1.78
