baz-snow-ss/Voron-2.4-R2/STL/Klicky-Probe-/Base_STL/Base_STL/Longer_probe_pressfit_helper.stl

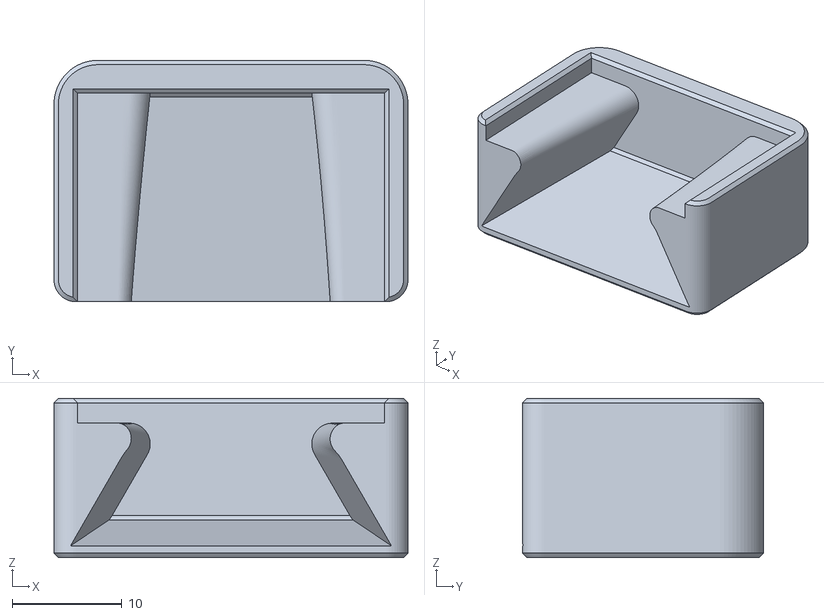
[picture p114: CAD file, 2023-06-08]
STL/Klicky-Probe-/Base_STL/Base_STL/Longer_probe_pressfit_helper.stl
32.3 x 22.0 x 14.5
