baz-snow-ss/Voron-2.4-R2/STL/Klicky-Probe-/Base_STL/Switch_extender.stl

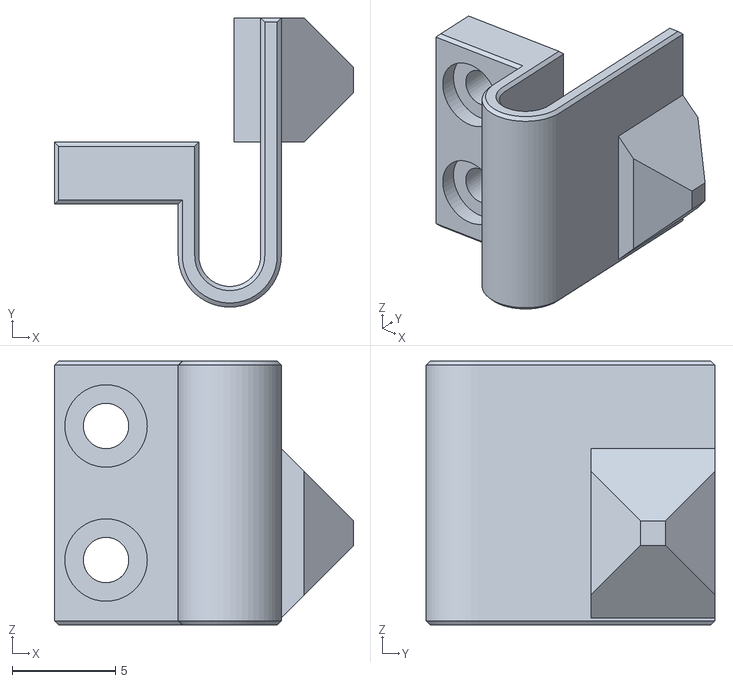
[picture p115: CAD file, 2023-06-08]
STL/Klicky-Probe-/Base_STL/Switch_extender.stl
14.5 x 14.0 x 12.8
