baz-snow-ss/Voron-2.4-R2/STL/LGX Stealthburner/Front_Body_V4.STL

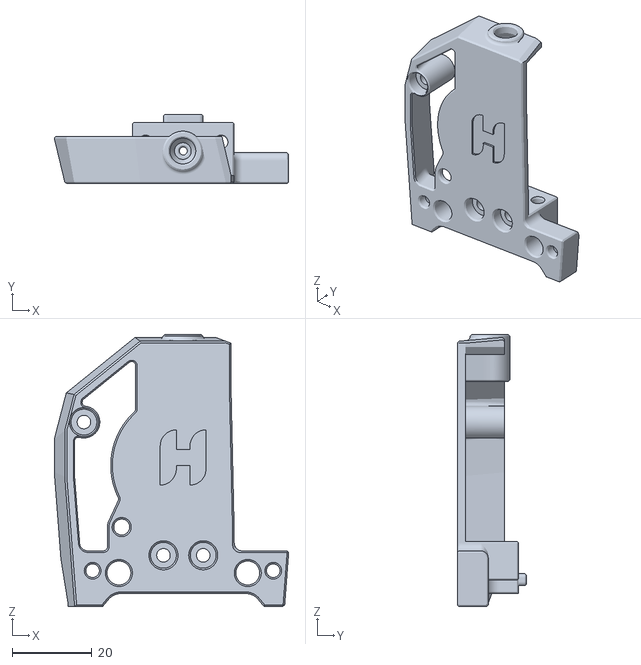
[picture p116: CAD file, 2023-06-07]
STL/LGX Stealthburner/Front_Body_V4.STL
59.0 x 17.4 x 68.4
