baz-snow-ss/Voron-2.4-R2/STL/logitech-c270/case_front_with_vents.stl

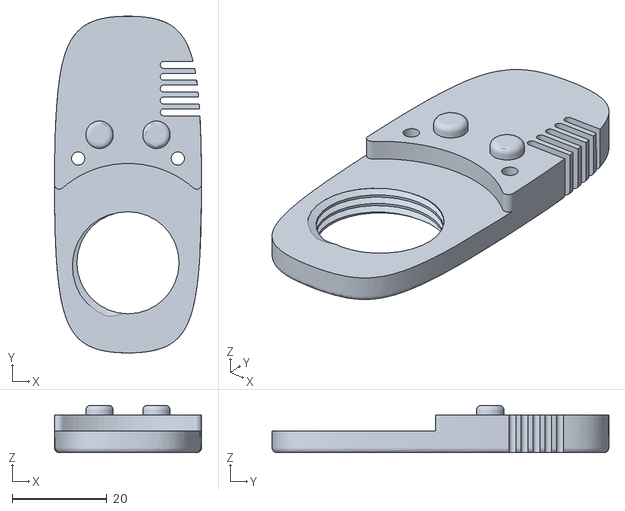
[picture p117: CAD file, 2023-06-07]
STL/logitech-c270/case_front_with_vents.stl
31.0 x 71.0 x 10.00
