baz-snow-ss/Voron-2.4-R2/STL/Nevermore_Micro-master/V5_Duo/Mods/RLF-35_by_Rama/Release_Nevermore-RLF35_Base.stp

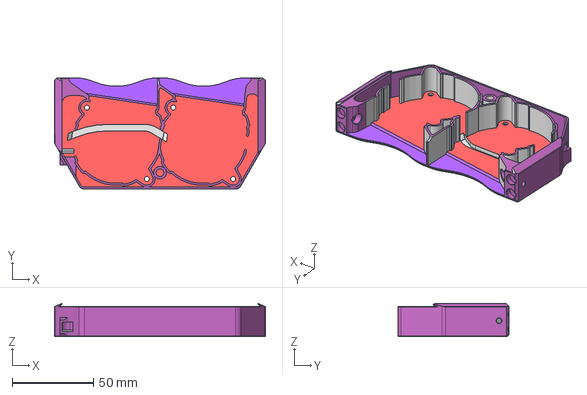
[picture p119: CAD file, 2023-06-08]
STL/Nevermore_Micro-master/V5_Duo/Mods/RLF-35_by_Rama/Release_Nevermore-RLF35_Base.stp
130.0 x 68.6 x 20.6 mm
