baz-snow-ss/Voron-2.4-R2/STL/Klicky-Probe-/Base_STL/Base_STL/1mm_Spacer.stl

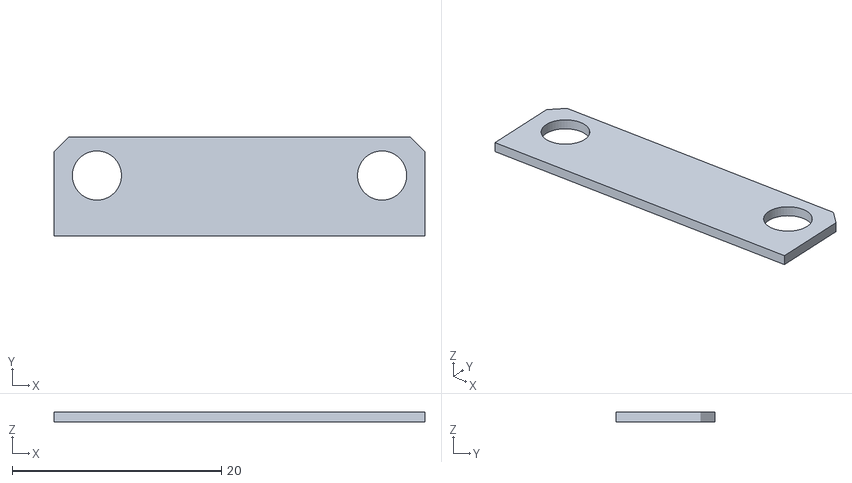
[picture p120: CAD file, 2023-06-08]
STL/Klicky-Probe-/Base_STL/Base_STL/1mm_Spacer.stl
35.5 x 9.50 x 1.00
