baz-snow-ss/Voron-2.4-R2/STL/LGX Stealthburner/Rear_Body_V3.STL

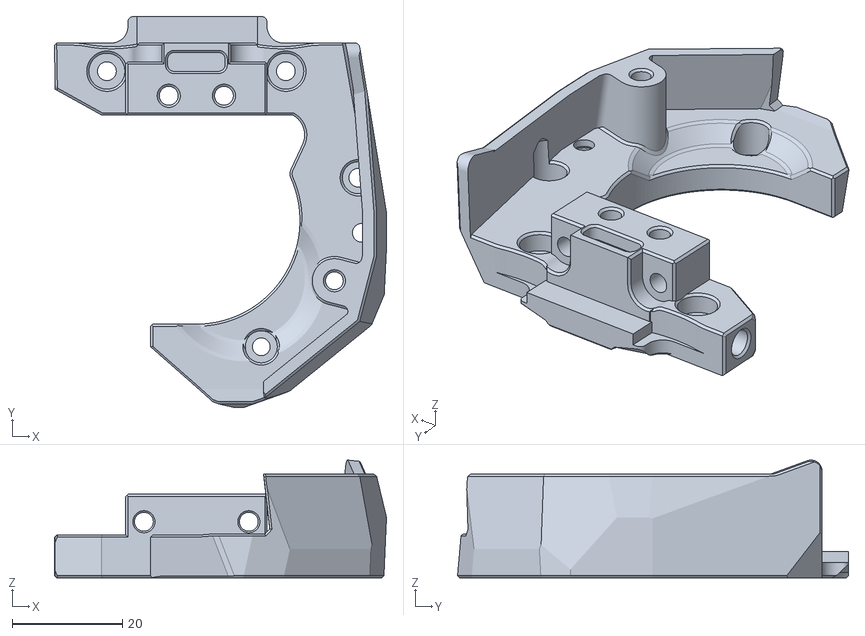
[picture p121: CAD file, 2023-06-07]
STL/LGX Stealthburner/Rear_Body_V3.STL
60.1 x 70.8 x 21.3
