baz-snow-ss/Voron-2.4-R2/STL/Nevermore_Micro-master/V4/V4_4x6_magnets/FAN_PLENUM_4_6.stl.stl

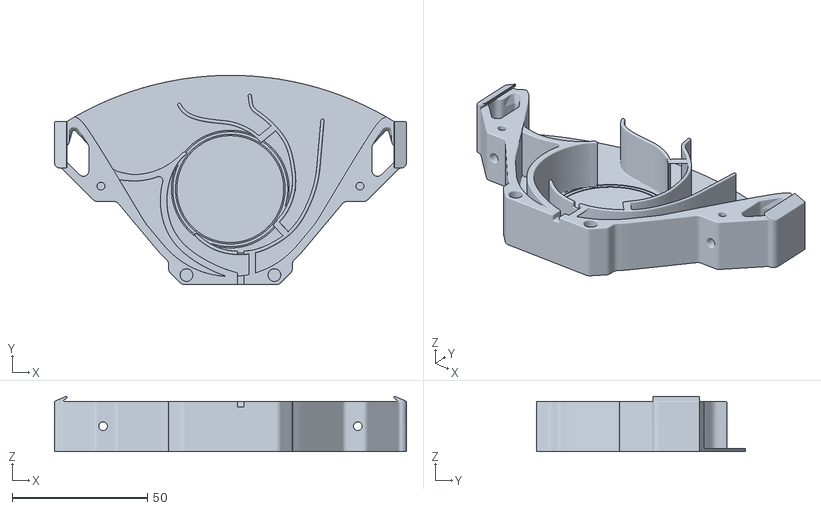
[picture p122: CAD file, 2023-06-08]
STL/Nevermore_Micro-master/V4/V4_4x6_magnets/FAN_PLENUM_4_6.stl.stl
130.0 x 77.3 x 20.5
