baz-snow-ss/Voron-2.4-R2/STL/Nevermore_Micro-master/V4/V4_6x3_magnets/FAN_PLENUM_LID_6_3.stl

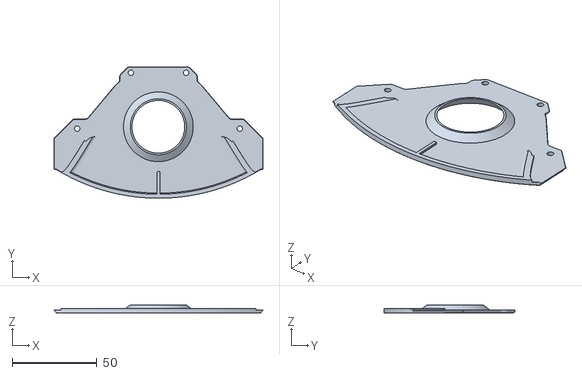
[picture p123: CAD file, 2023-06-08]
STL/Nevermore_Micro-master/V4/V4_6x3_magnets/FAN_PLENUM_LID_6_3.stl
123.0 x 77.3 x 4.80
