baz-snow-ss/Voron-2.4-R2/STL/2020_Extrusion_profile_cover/files/2020_Extrusion_profile_cover.step

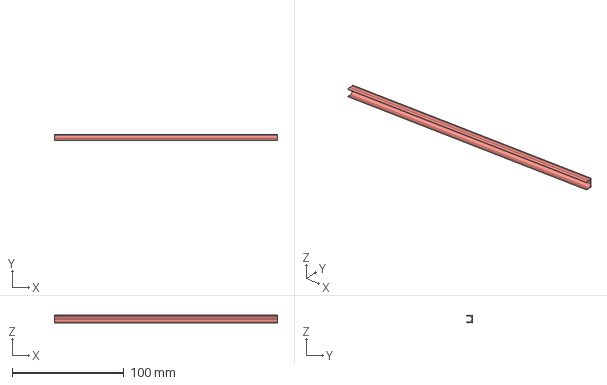
[picture p124: CAD file, 2023-06-07]
STL/2020_Extrusion_profile_cover/files/2020_Extrusion_profile_cover.step
200.0 x 5.10 x 7.00 mm
