baz-snow-ss/Voron-2.4-R2/STL/LGX Stealthburner/Stealthburner_Body_V12.STL

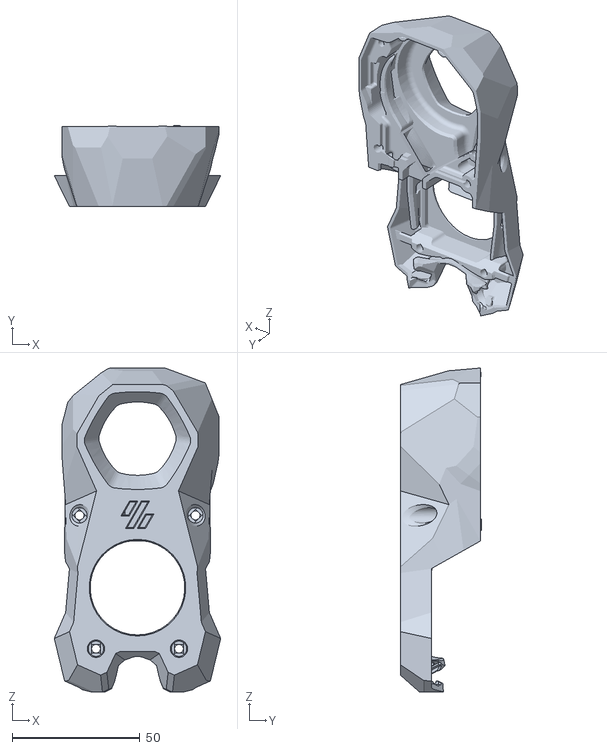
[picture p125: CAD file, 2023-06-07]
STL/LGX Stealthburner/Stealthburner_Body_V12.STL
65.1 x 31.8 x 126.8
