baz-snow-ss/Voron-2.4-R2/STL/Nevermore_Micro-master/V4/V4_4x6_magnets/FILTER_CARTRIDGE_6_3_DirectedUp.stl

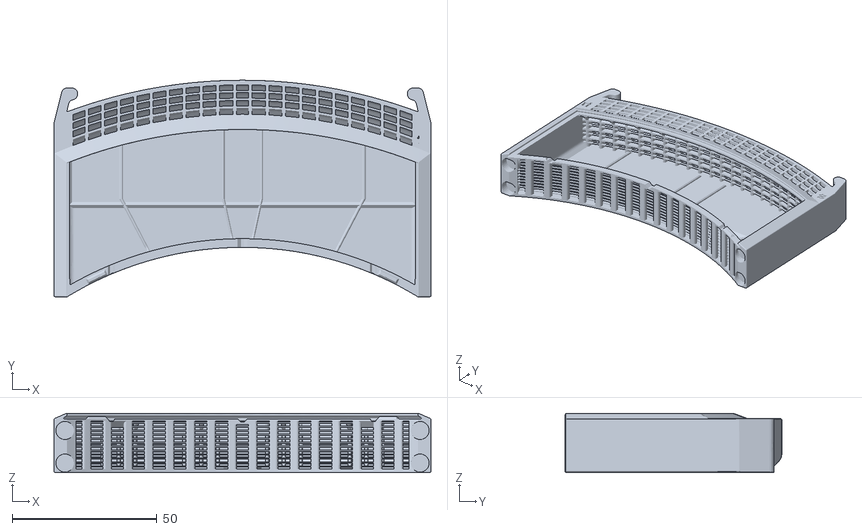
[picture p126: CAD file, 2023-06-08]
STL/Nevermore_Micro-master/V4/V4_4x6_magnets/FILTER_CARTRIDGE_6_3_DirectedUp.stl
130.0 x 74.7 x 20.5
