baz-snow-ss/Voron-2.4-R2/STL/Klicky-Probe-/Base_STL/Base_STL/KlickyProbe_v2.stl

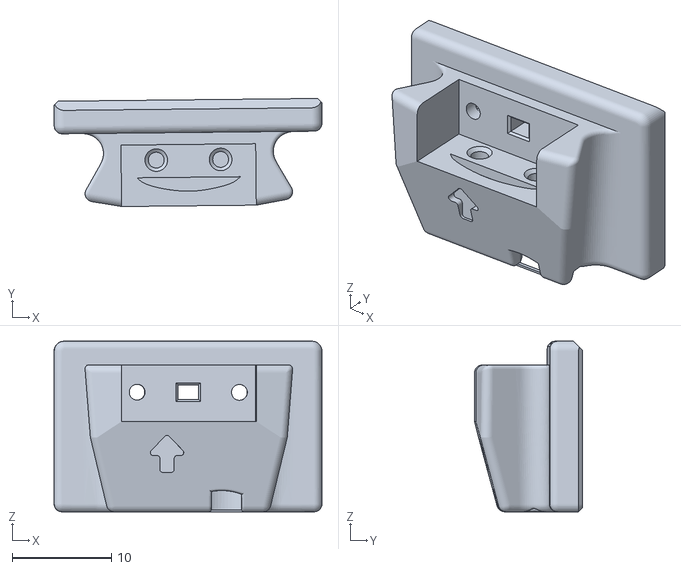
[picture p127: CAD file, 2023-06-08]
STL/Klicky-Probe-/Base_STL/Base_STL/KlickyProbe_v2.stl
27.1 x 10.9 x 17.2
