baz-snow-ss/Voron-2.4-R2/STL/LGX Stealthburner/Cable_Cover_V22.STL

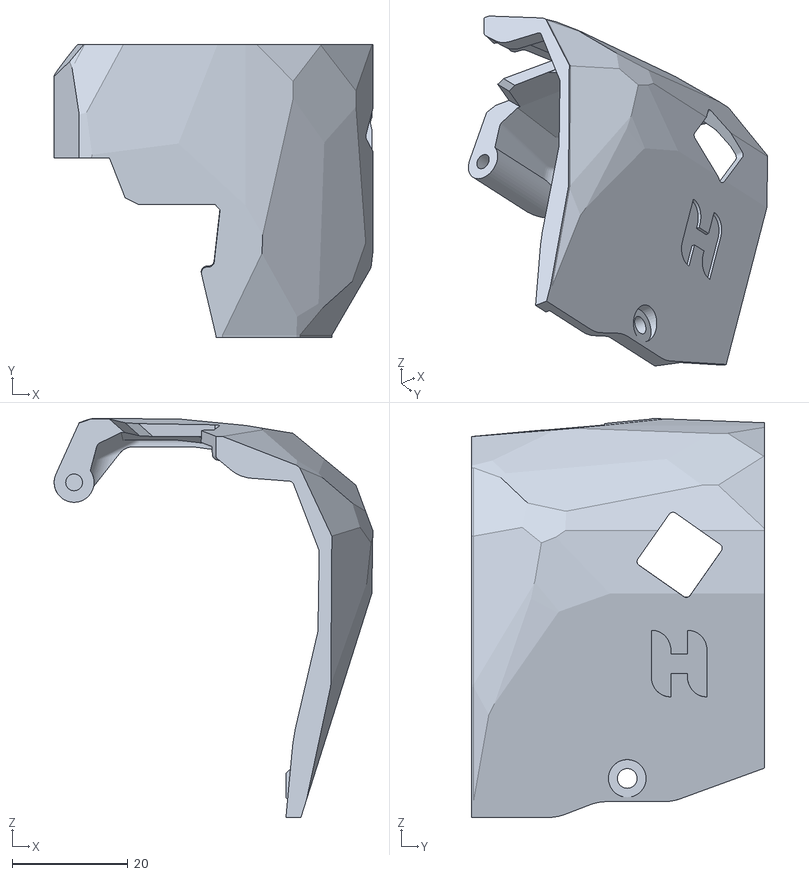
[picture p128: CAD file, 2023-06-07]
STL/LGX Stealthburner/Cable_Cover_V22.STL
55.0 x 50.6 x 68.9
