baz-snow-ss/Voron-2.4-R2/STL/Klicky-Probe-/Base_STL/Base_STL/Probe_pressfit_holder.stl

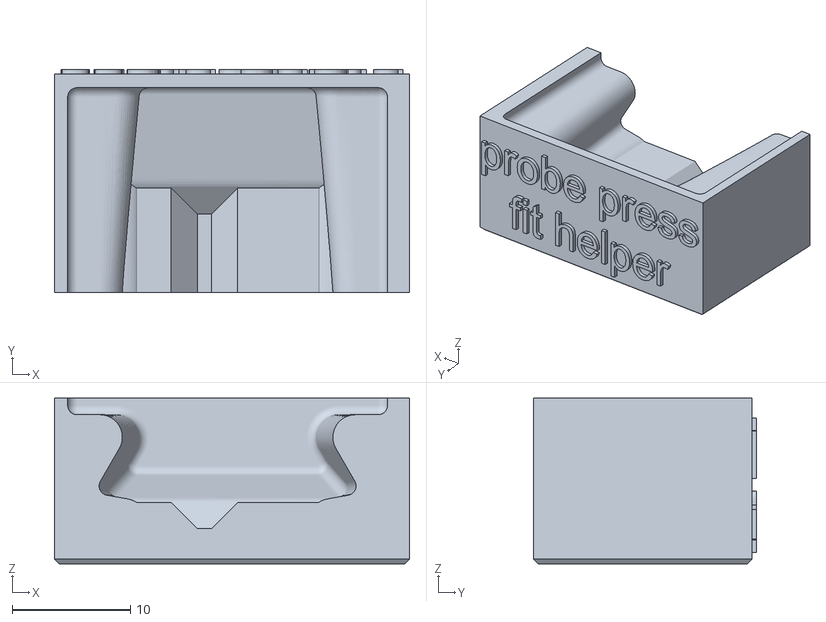
[picture p129: CAD file, 2023-06-08]
STL/Klicky-Probe-/Base_STL/Base_STL/Probe_pressfit_holder.stl
30.0 x 18.9 x 14.0
