baz-snow-ss/Voron-2.4-R2/STL/LGX Stealthburner/Chain_Anchor_3_Hole_V2.STL

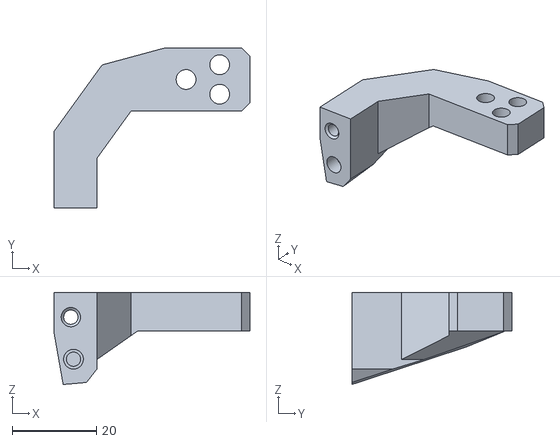
[picture p130: CAD file, 2023-06-07]
STL/LGX Stealthburner/Chain_Anchor_3_Hole_V2.STL
46.6 x 38.0 x 21.9
